rusefi/uaefi/boards/uaefi-a/board/-Produce_DanZhi.SMT_Snapshot.Bottom.2582135A_Y375.SMT02312031502790.png

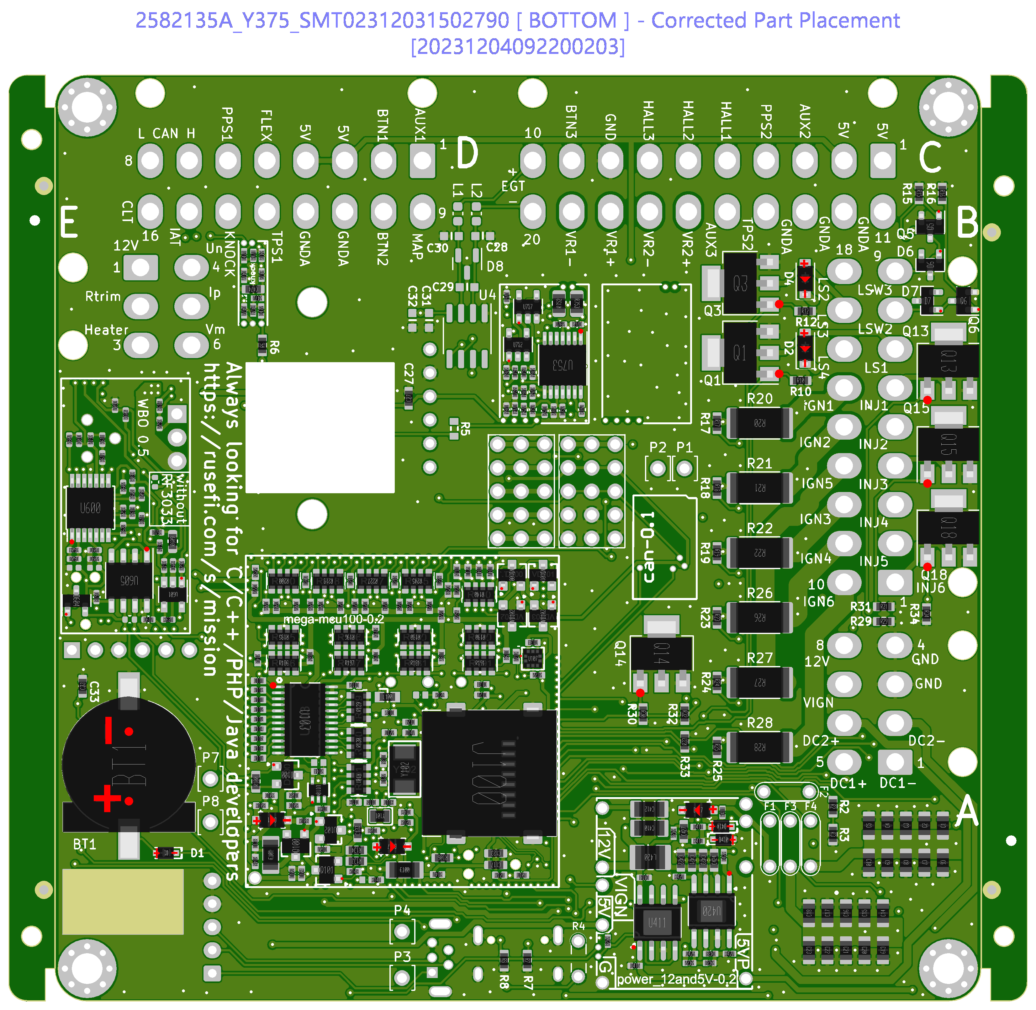
boards/uaefi-a/board/-Produce_DanZhi.SMT_Snapshot.Bottom.2582135A_Y375.SMT02312031502790.png
