rusefi/uaefi/boards/uaefi-a/board/misc/uaefi-a-bottom.png

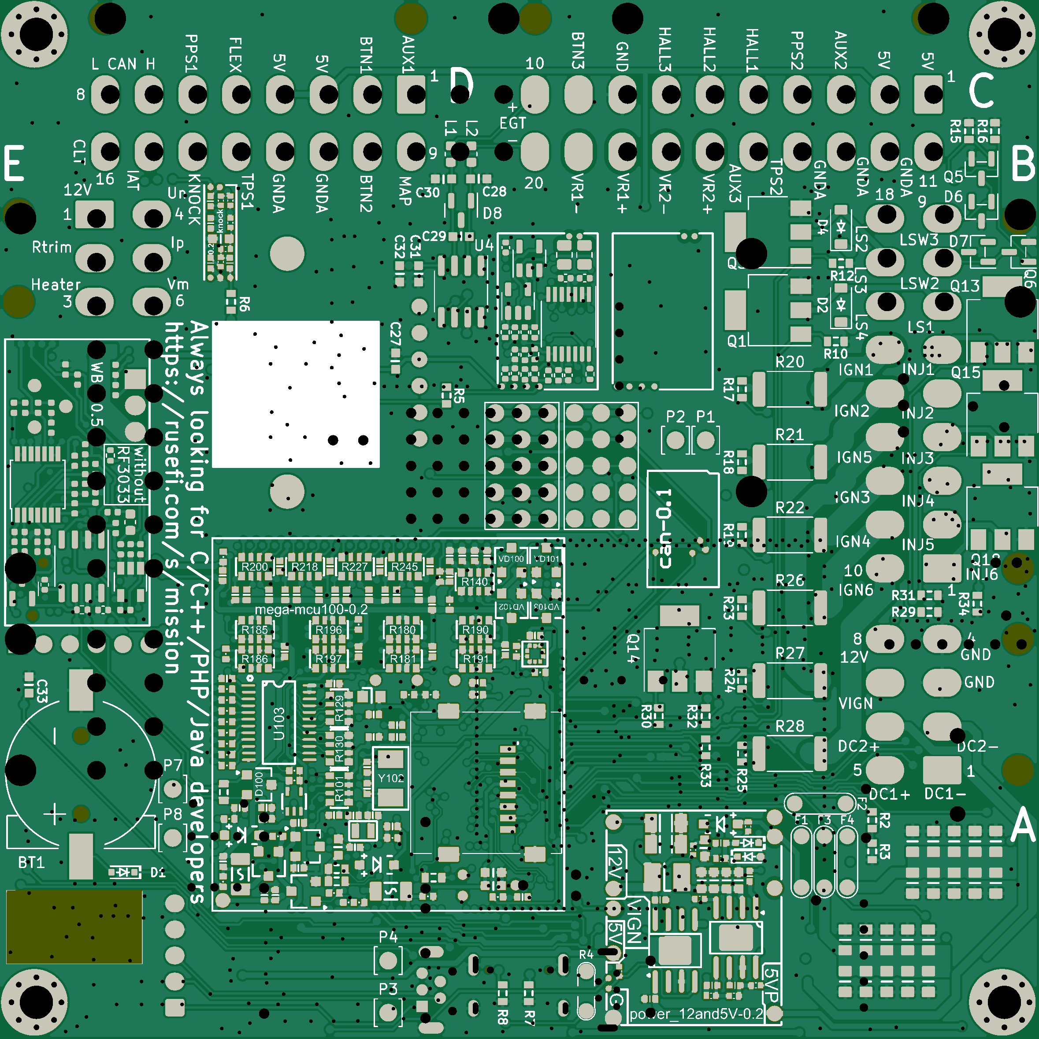
boards/uaefi-a/board/misc/uaefi-a-bottom.png
