rusefi/uaefi/boards/uaefi-a/board/misc/uaefi-a-top.png

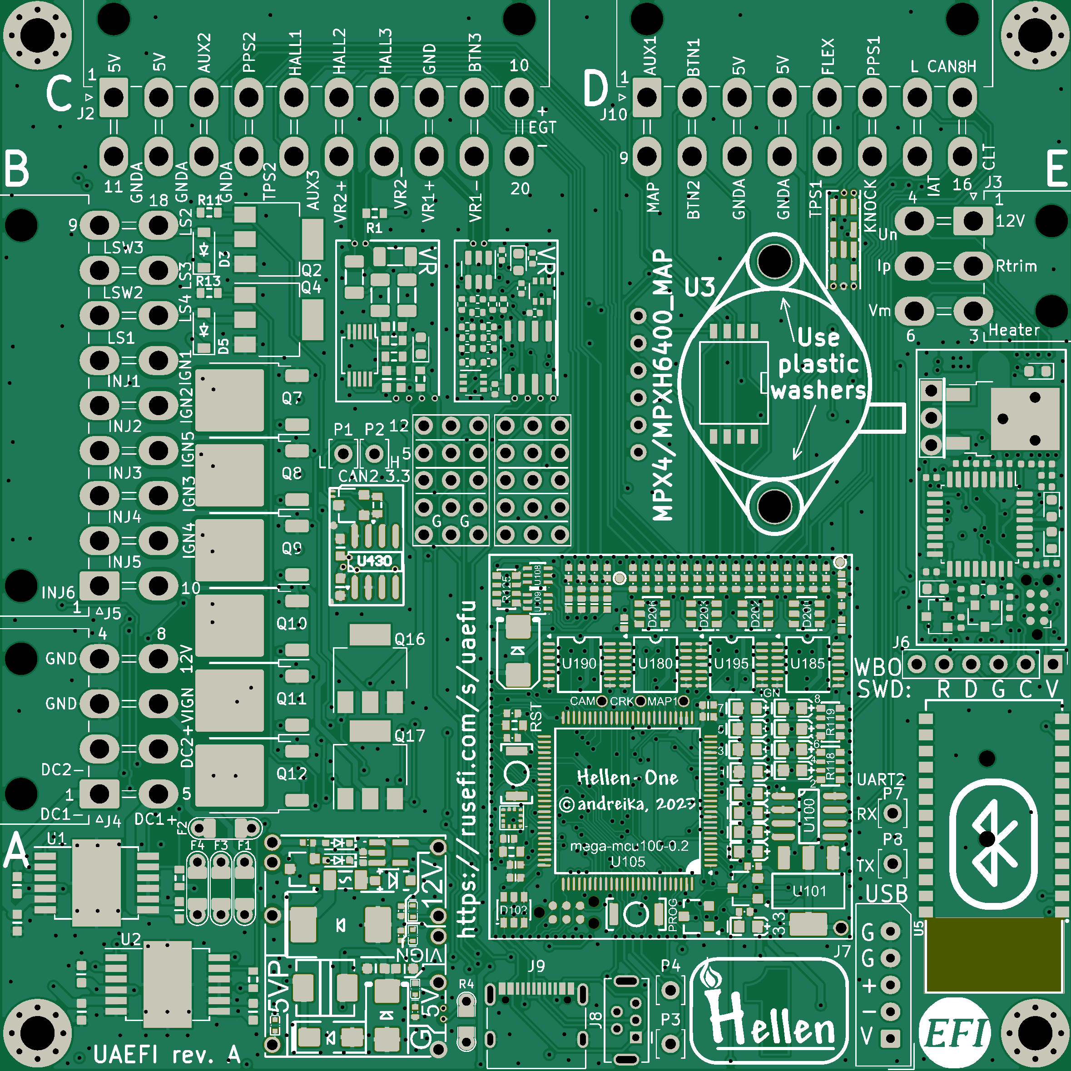
boards/uaefi-a/board/misc/uaefi-a-top.png
