rusefi/uaefi/boards/uaefi-a/board/uaefi-a.png

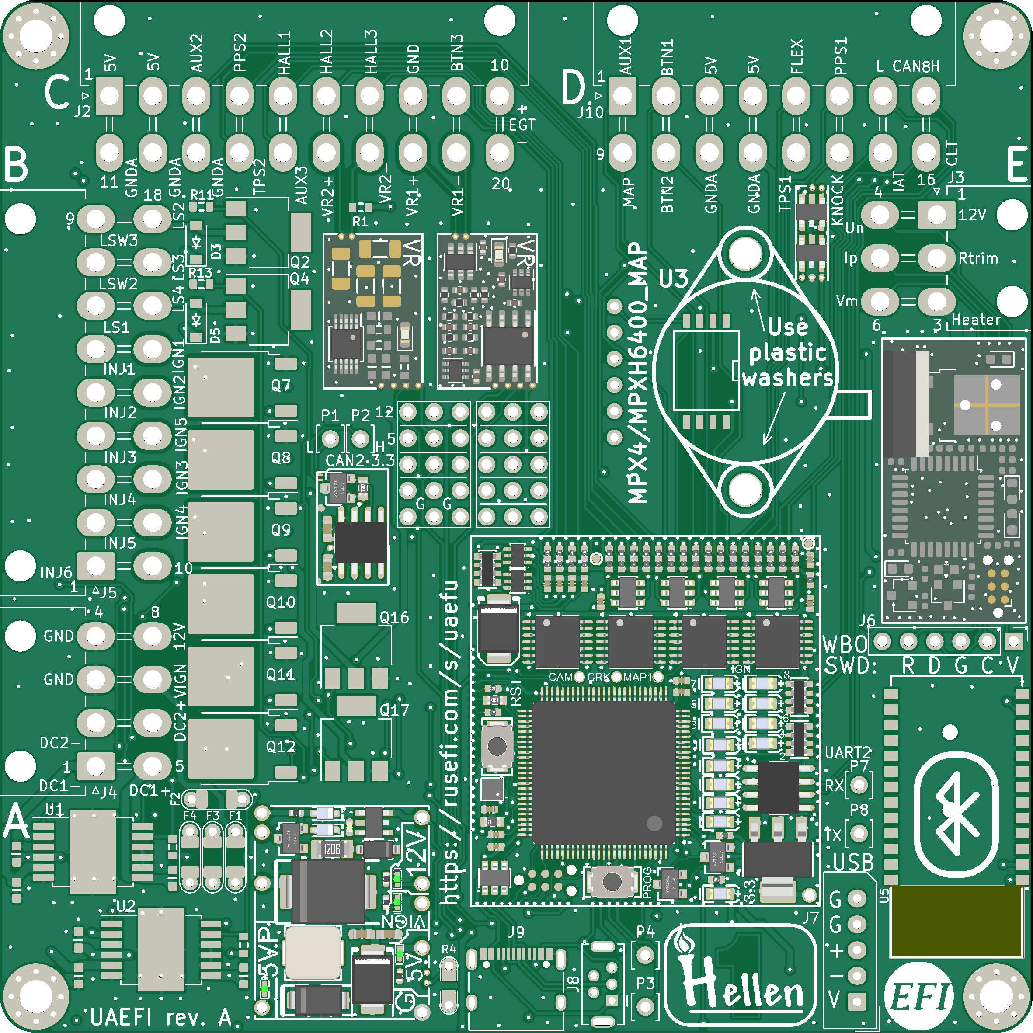
boards/uaefi-a/board/uaefi-a.png
