rusefi/uaefi/boards/uaefi-b/board/misc/uaefi-b-bottom.png

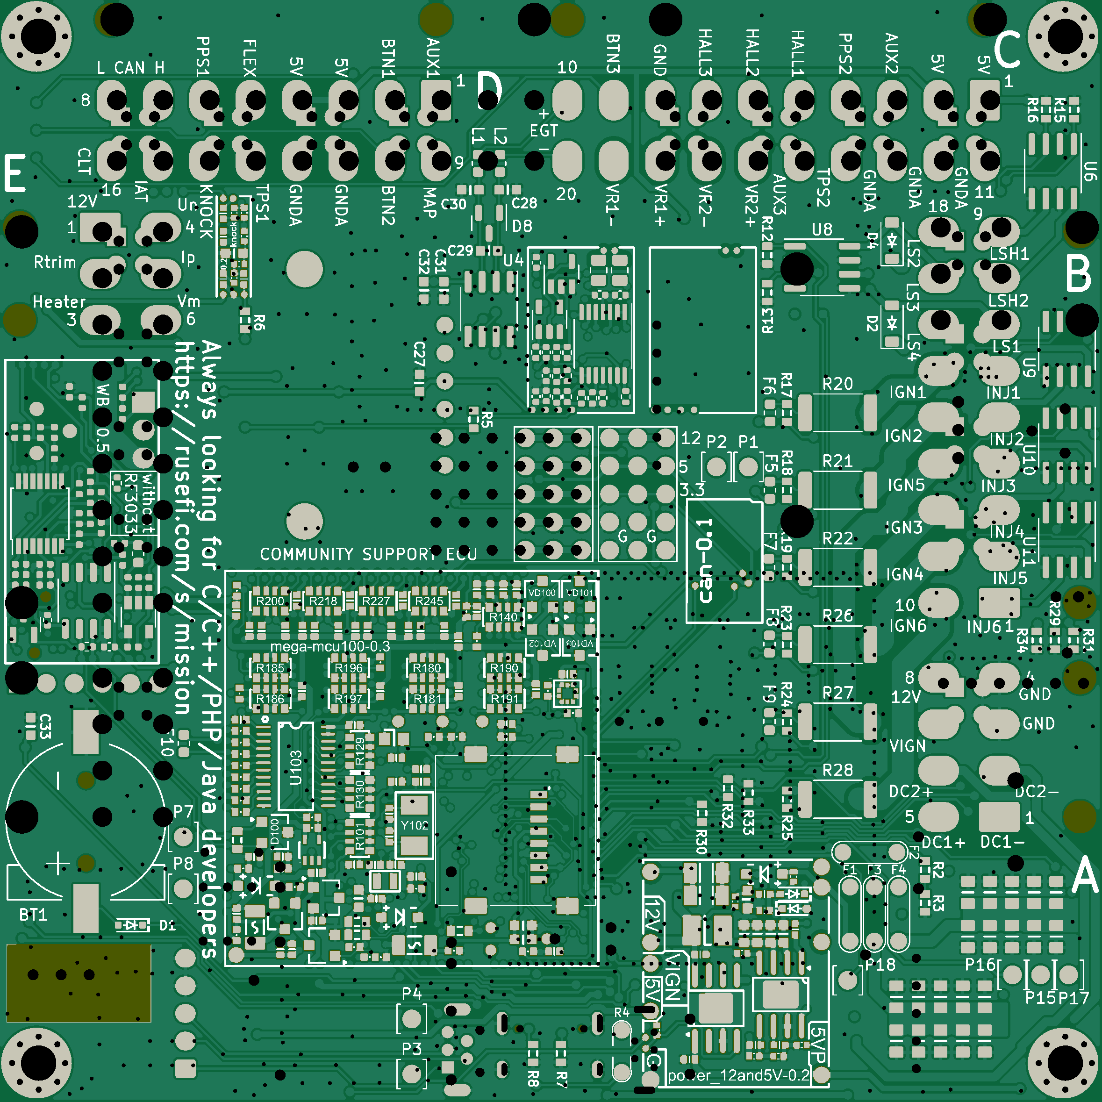
boards/uaefi-b/board/misc/uaefi-b-bottom.png
