rusefi/uaefi/boards/uaefi-b/board/misc/uaefi-b-outline.png

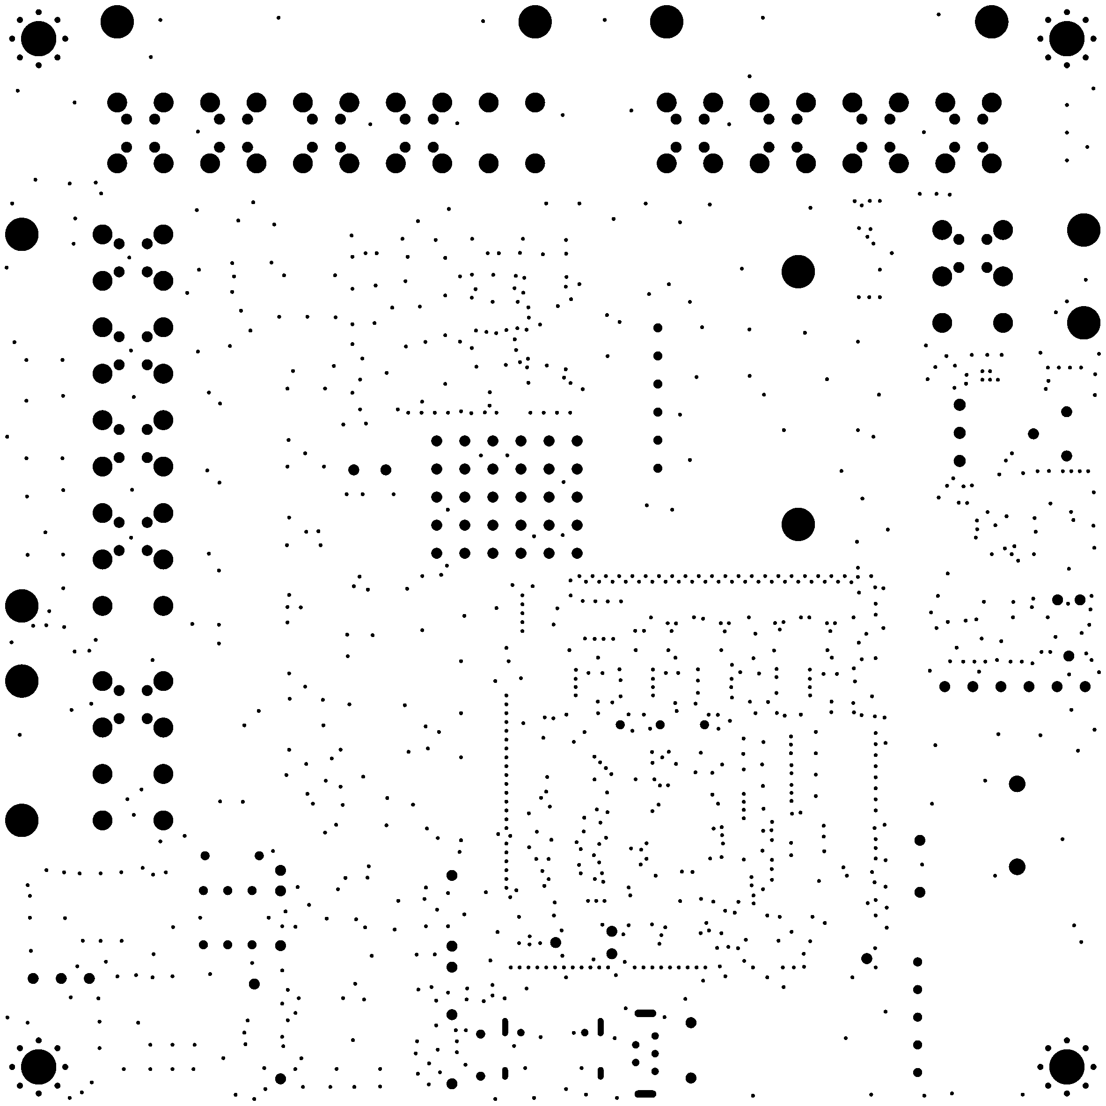
boards/uaefi-b/board/misc/uaefi-b-outline.png
