rusefi/uaefi/boards/uaefi-b/board/misc/uaefi-b-top.png

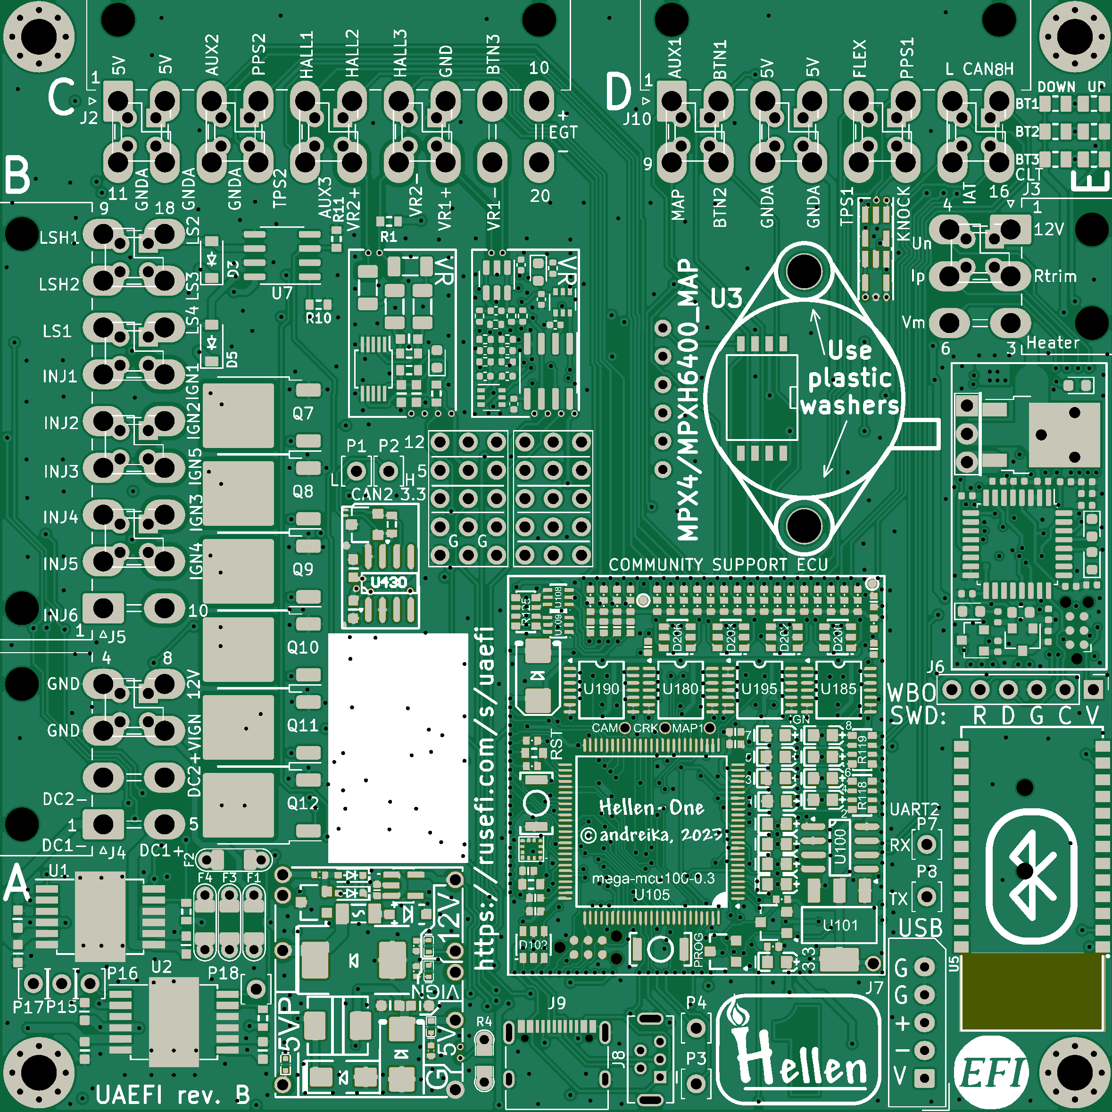
boards/uaefi-b/board/misc/uaefi-b-top.png
