rusefi/uaefi/boards/uaefi-b/board/Produce_DanZhi.SMT_Original_Snapshot.Top.2582135A_Y401.SMT02402061592675.png

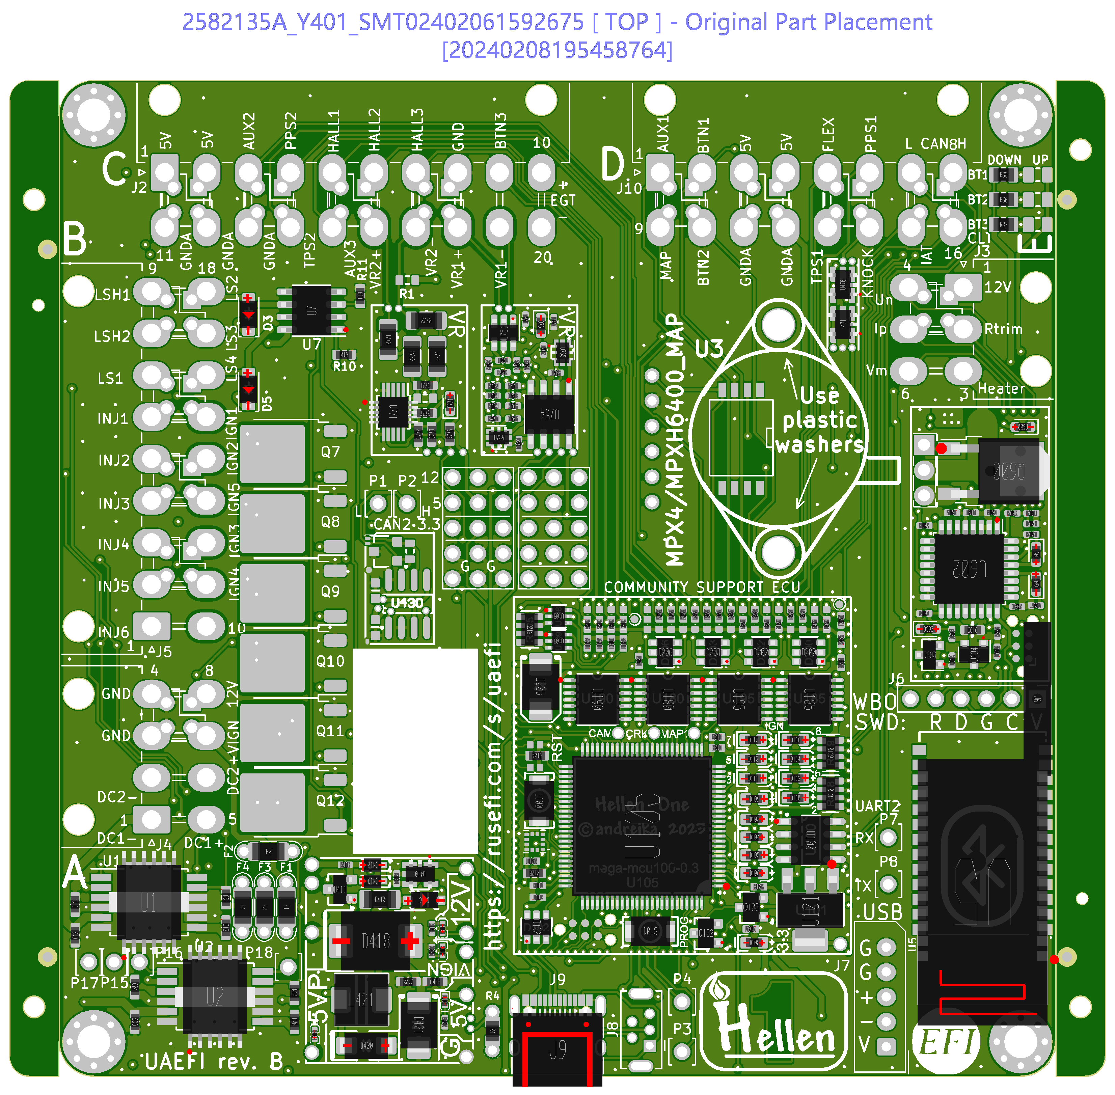
boards/uaefi-b/board/Produce_DanZhi.SMT_Original_Snapshot.Top.2582135A_Y401.SMT02402061592675.png
