rusefi/uaefi/boards/uaefi-b/board/uaefi-b.png

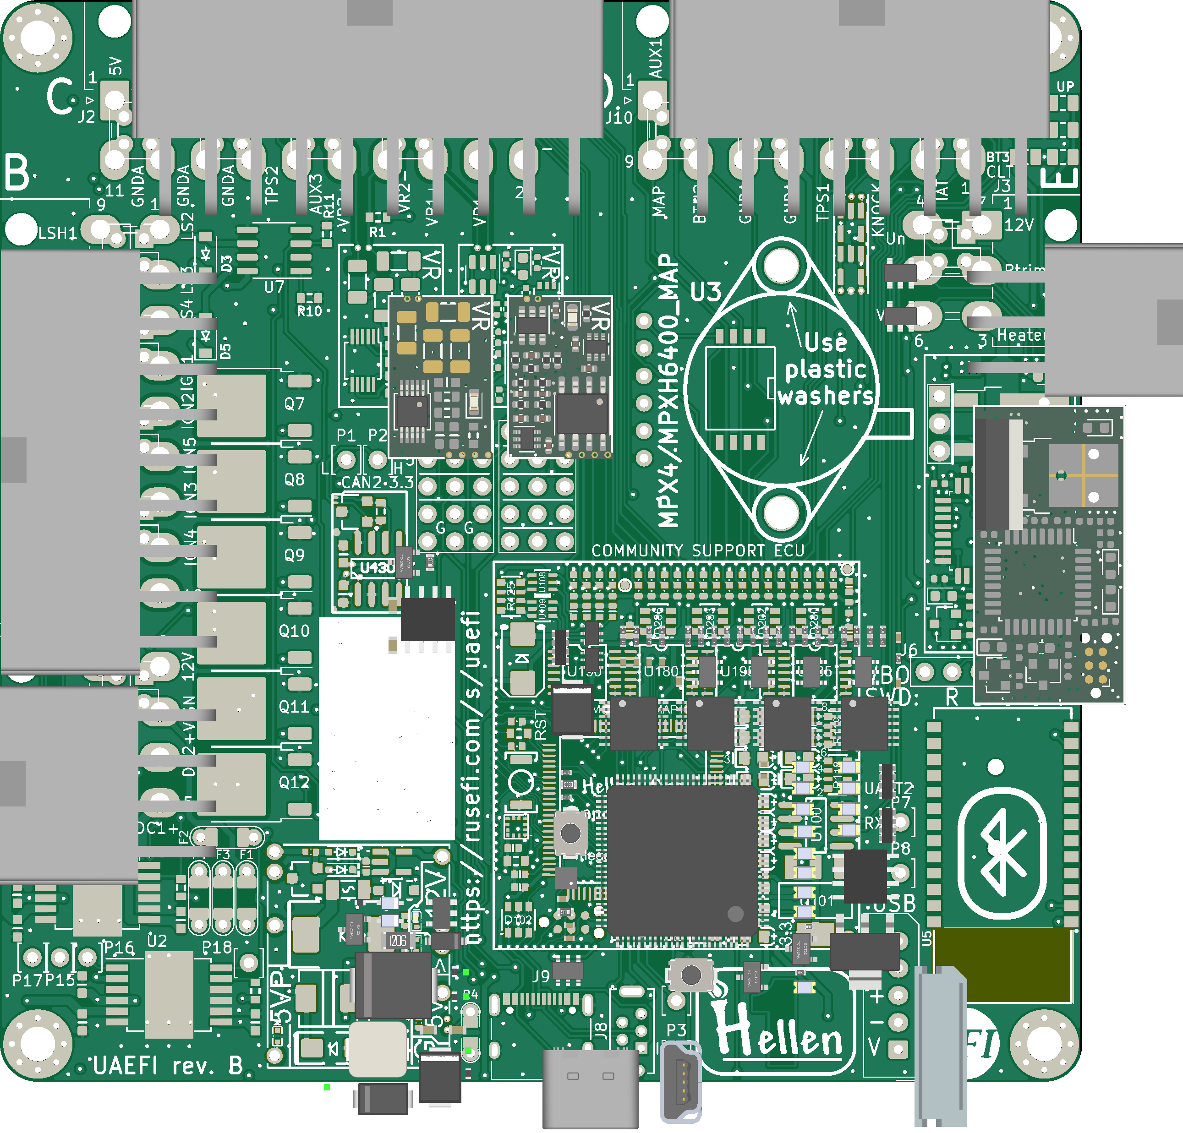
boards/uaefi-b/board/uaefi-b.png
