rusefi/uaefi/boards/uaefi-c/board/misc/uaefi-c-bottom.png

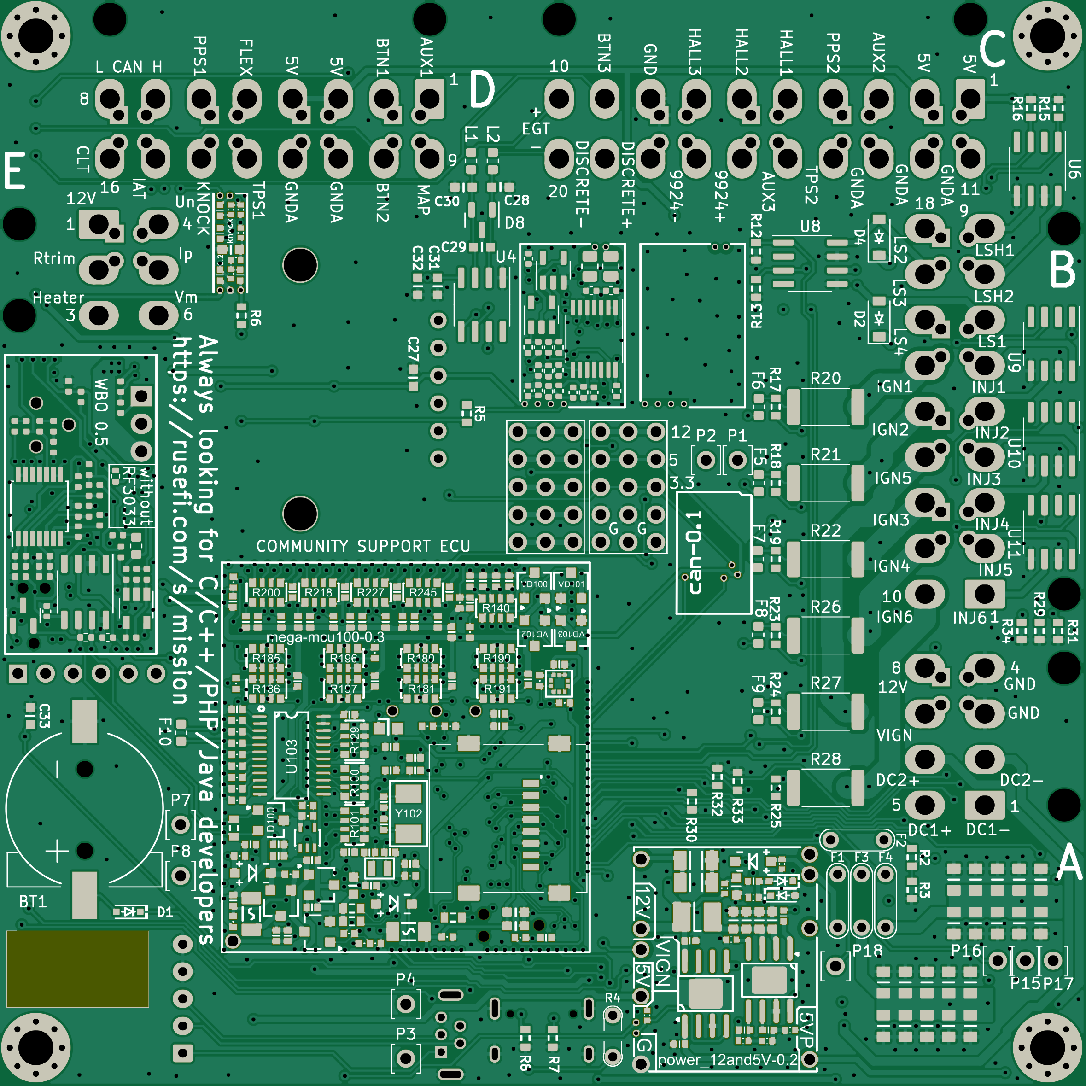
boards/uaefi-c/board/misc/uaefi-c-bottom.png
