rusefi/uaefi/boards/uaefi-c/board/misc/uaefi-c-top.png

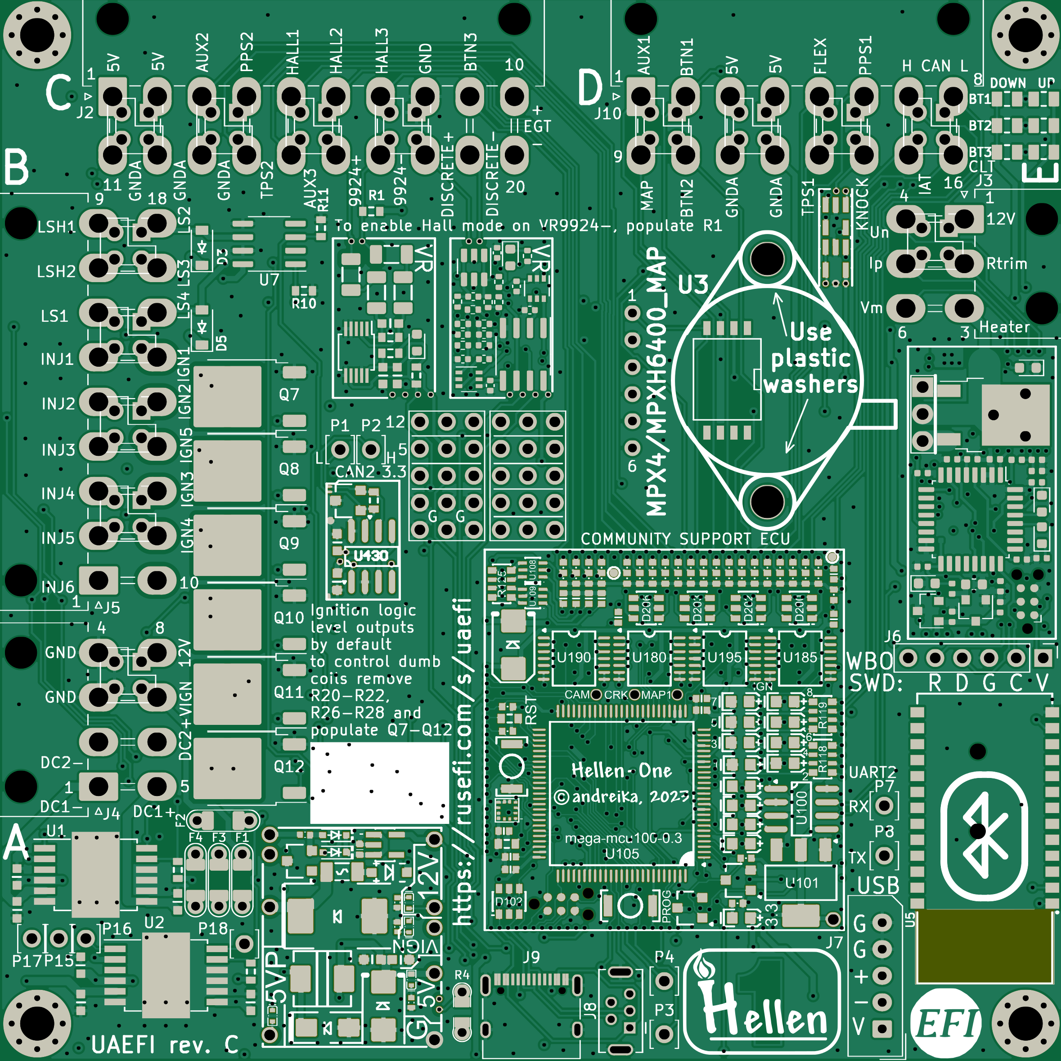
boards/uaefi-c/board/misc/uaefi-c-top.png
