rusefi/uaefi/boards/uaefi-c/board/Original_Snapshot.Top.2582135A_Y427.SMT02404051683002.png

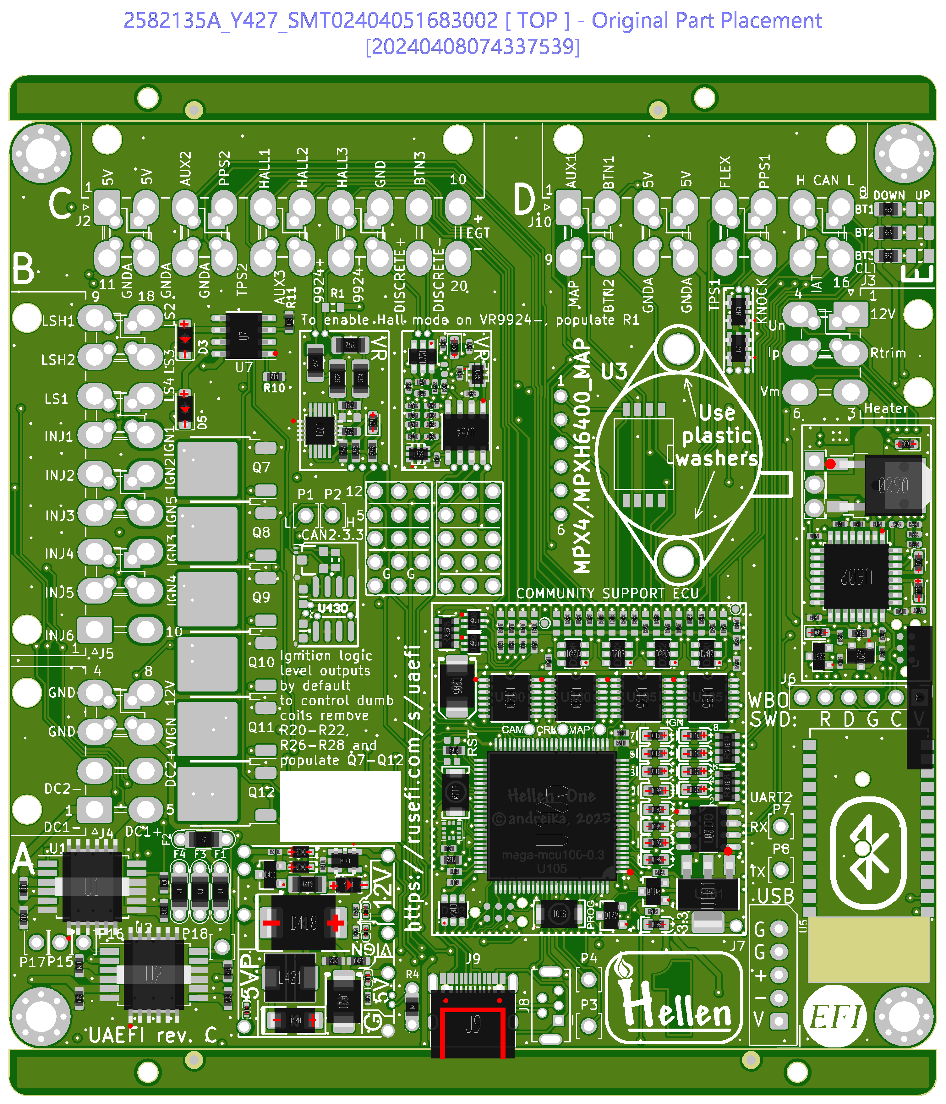
boards/uaefi-c/board/Original_Snapshot.Top.2582135A_Y427.SMT02404051683002.png
