rusefi/uaefi/boards/uaefi-c/board/Produce_DanZhi.SMT_Snapshot.Bottom.2582135A_Y427.SMT02404051683002.png

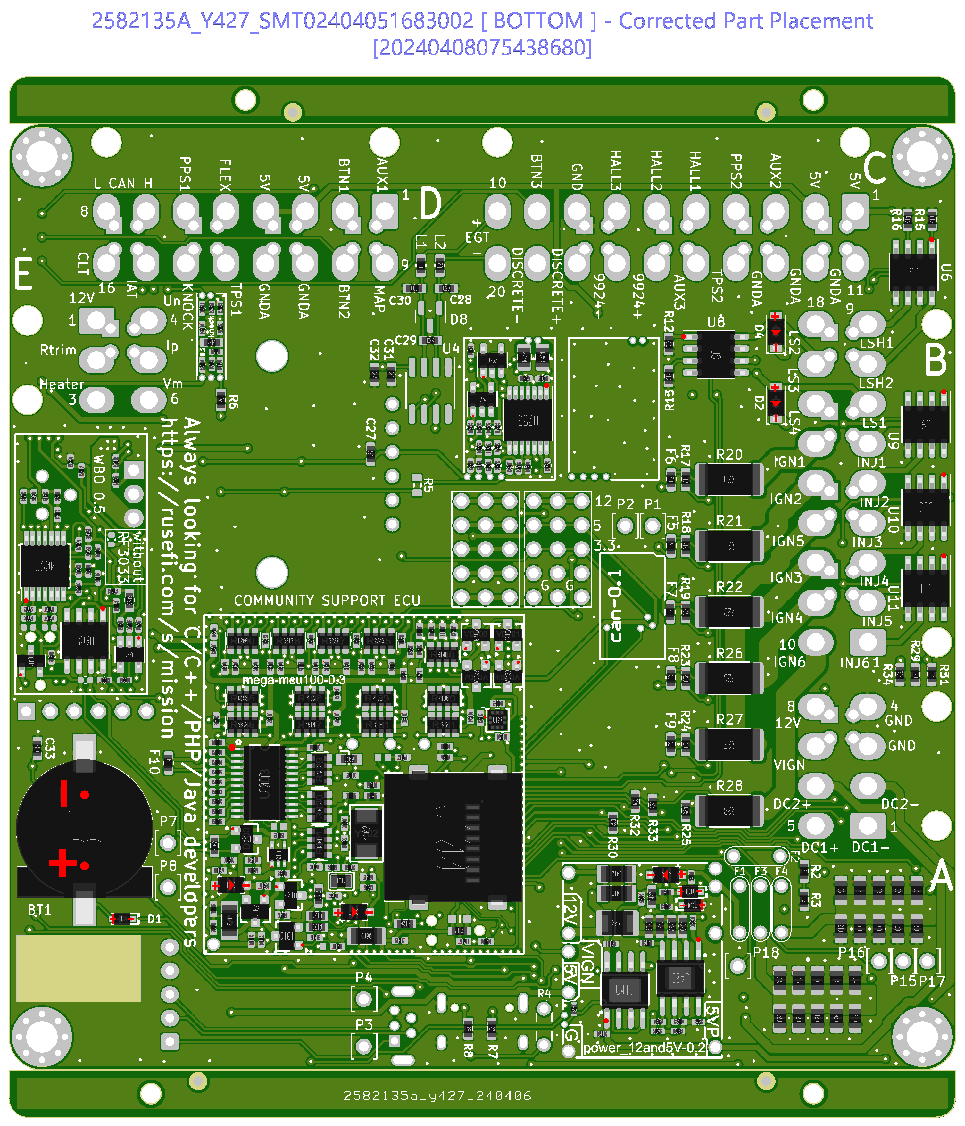
boards/uaefi-c/board/Produce_DanZhi.SMT_Snapshot.Bottom.2582135A_Y427.SMT02404051683002.png
