rusefi/uaefi/boards/uaefi-c/board/uaefi-c.png

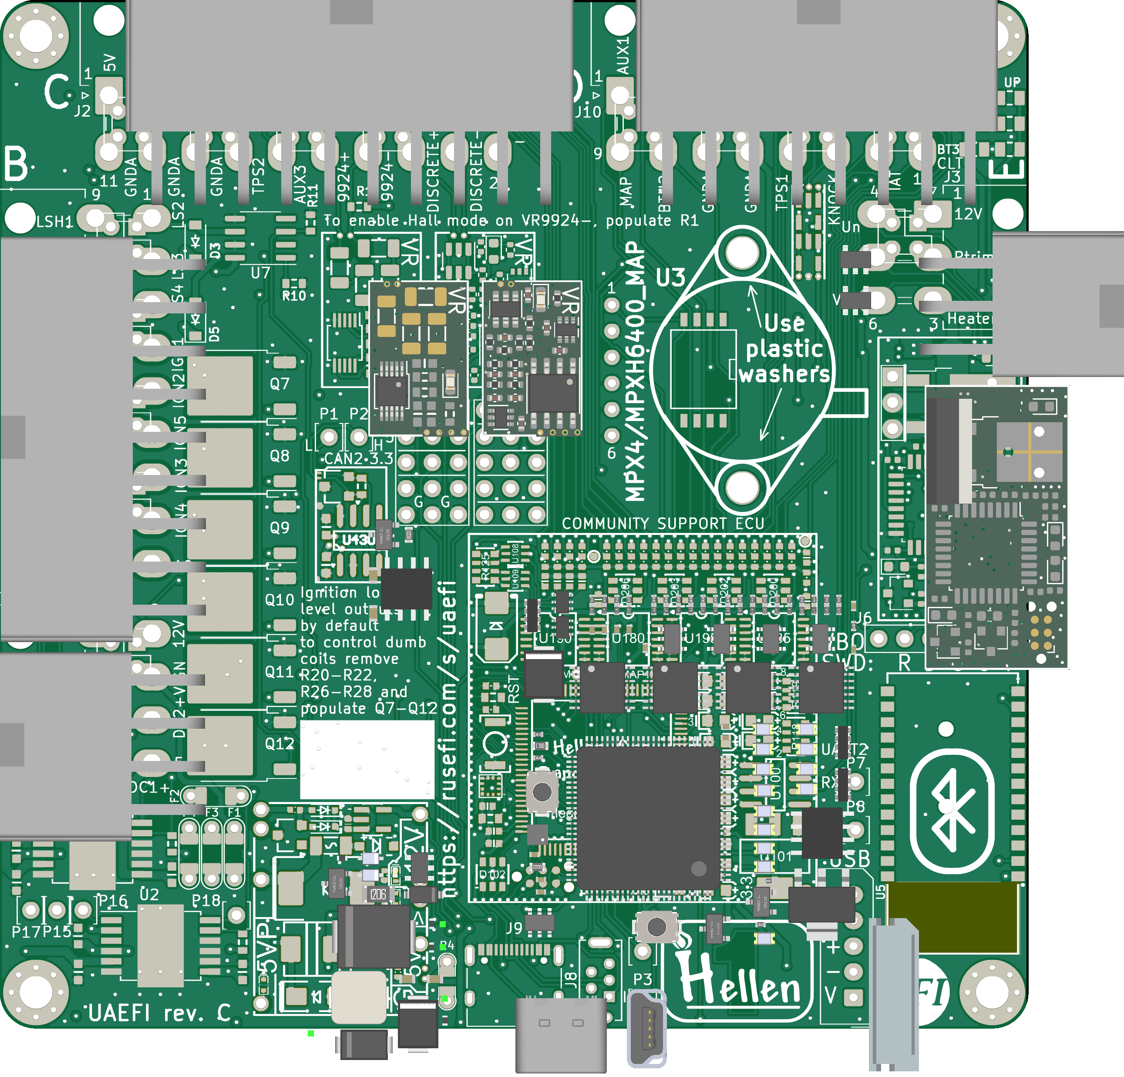
boards/uaefi-c/board/uaefi-c.png
