rusefi/uaefi/boards/uaefi-d/board/160-Produce_DanZhi.SMT_Original_Snapshot.Top.2582135A_Y468.SMT02408161894510.png

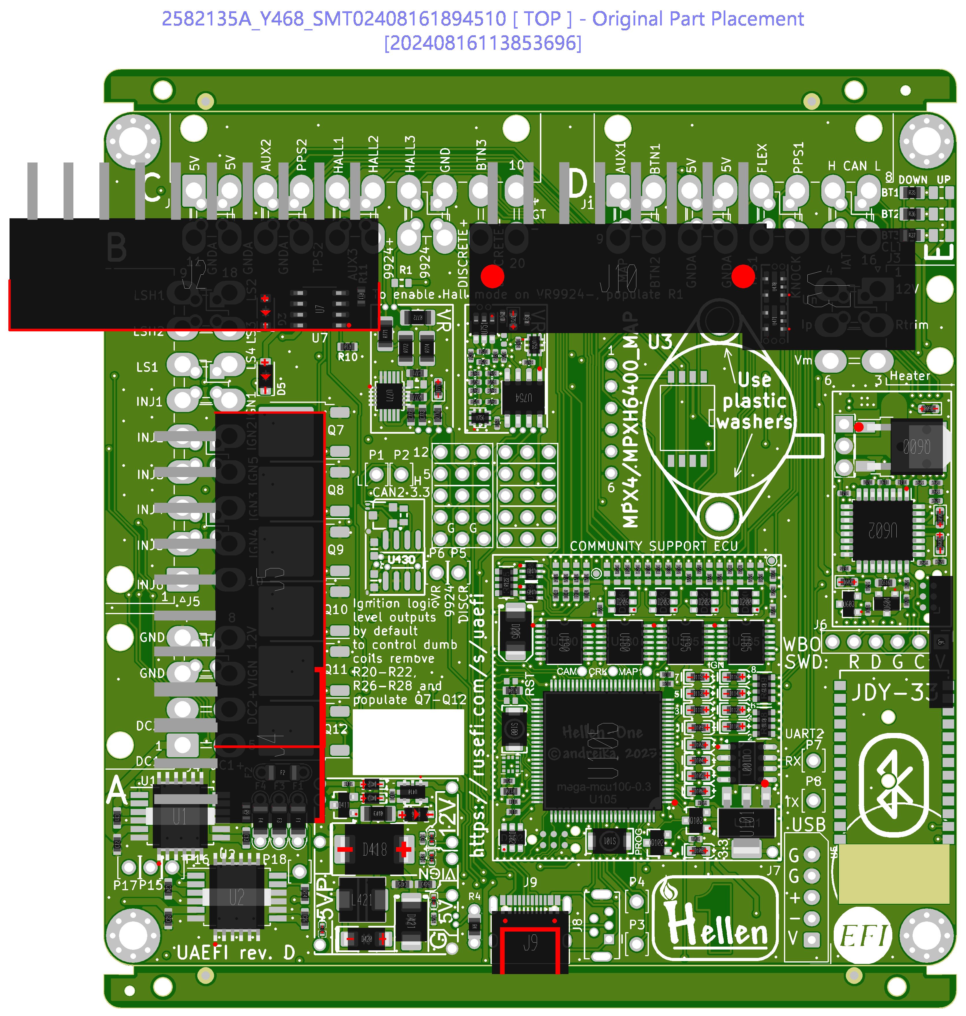
boards/uaefi-d/board/160-Produce_DanZhi.SMT_Original_Snapshot.Top.2582135A_Y468.SMT02408161894510.png
