rusefi/uaefi/boards/uaefi-d/board/119915741184-Produce_DanZhi.SMT_Snapshot.Top.2582135A_Y468.SMT02408161894510.png

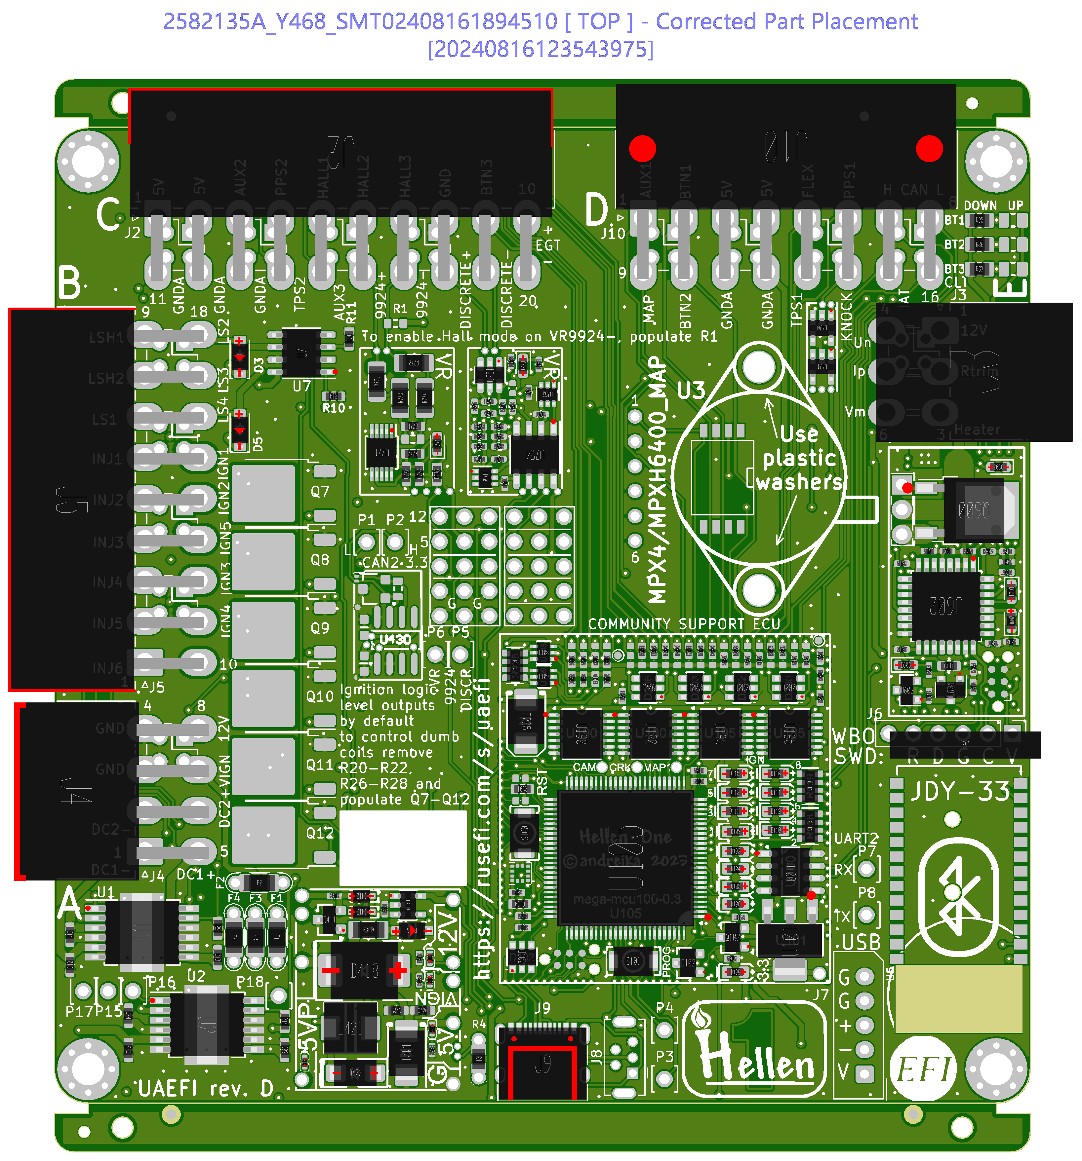
boards/uaefi-d/board/119915741184-Produce_DanZhi.SMT_Snapshot.Top.2582135A_Y468.SMT02408161894510.png
