rusefi/uaefi/boards/uaefi-d/board/-Produce_DanZhi.SMT_Original_Snapshot.Bottom.2582135A_Y468.SMT02408161894510.png

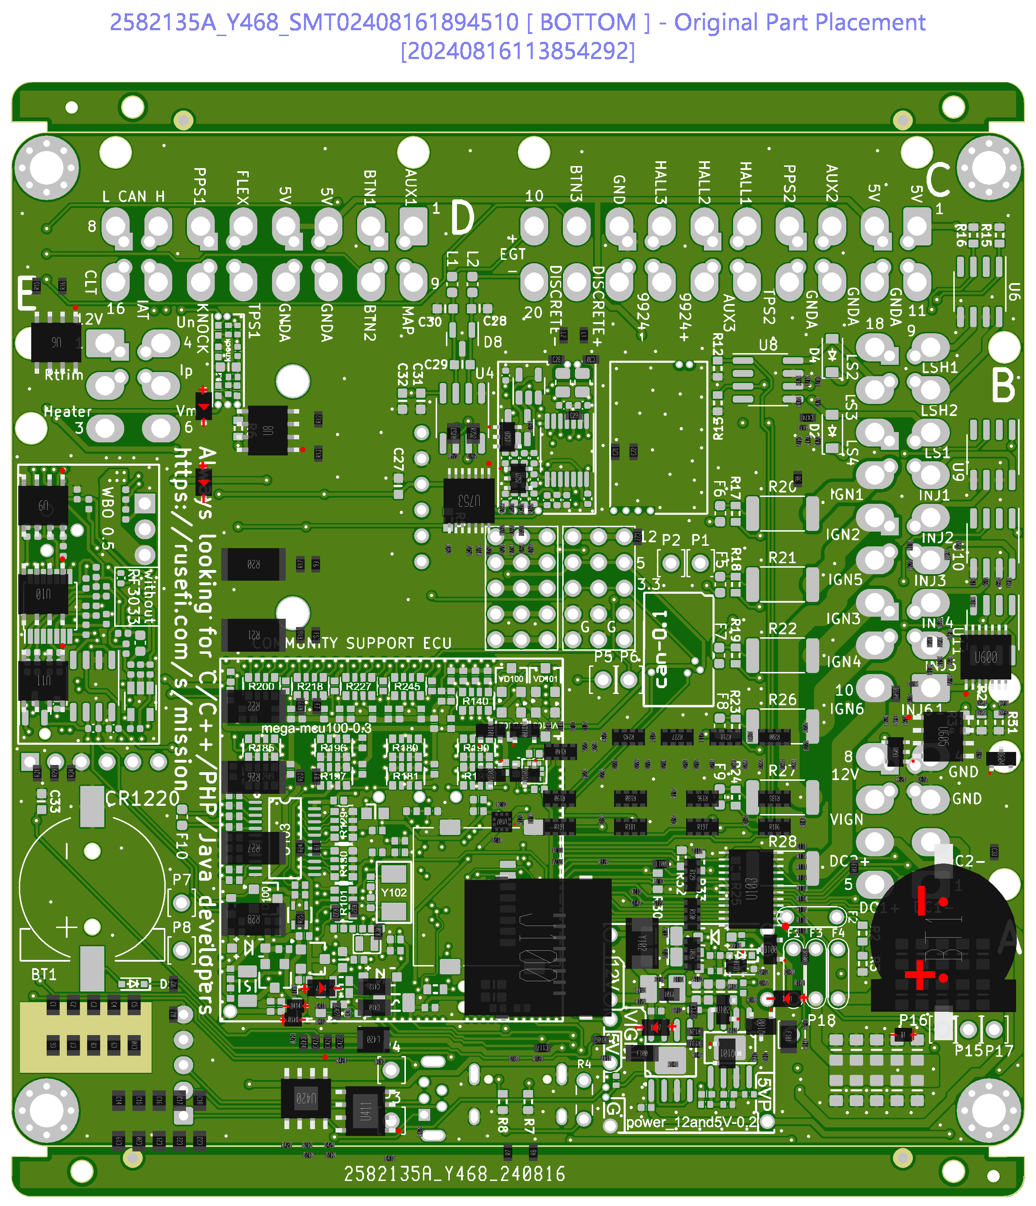
boards/uaefi-d/board/-Produce_DanZhi.SMT_Original_Snapshot.Bottom.2582135A_Y468.SMT02408161894510.png
