rusefi/uaefi/boards/uaefi-d/board/uaefi-d.png

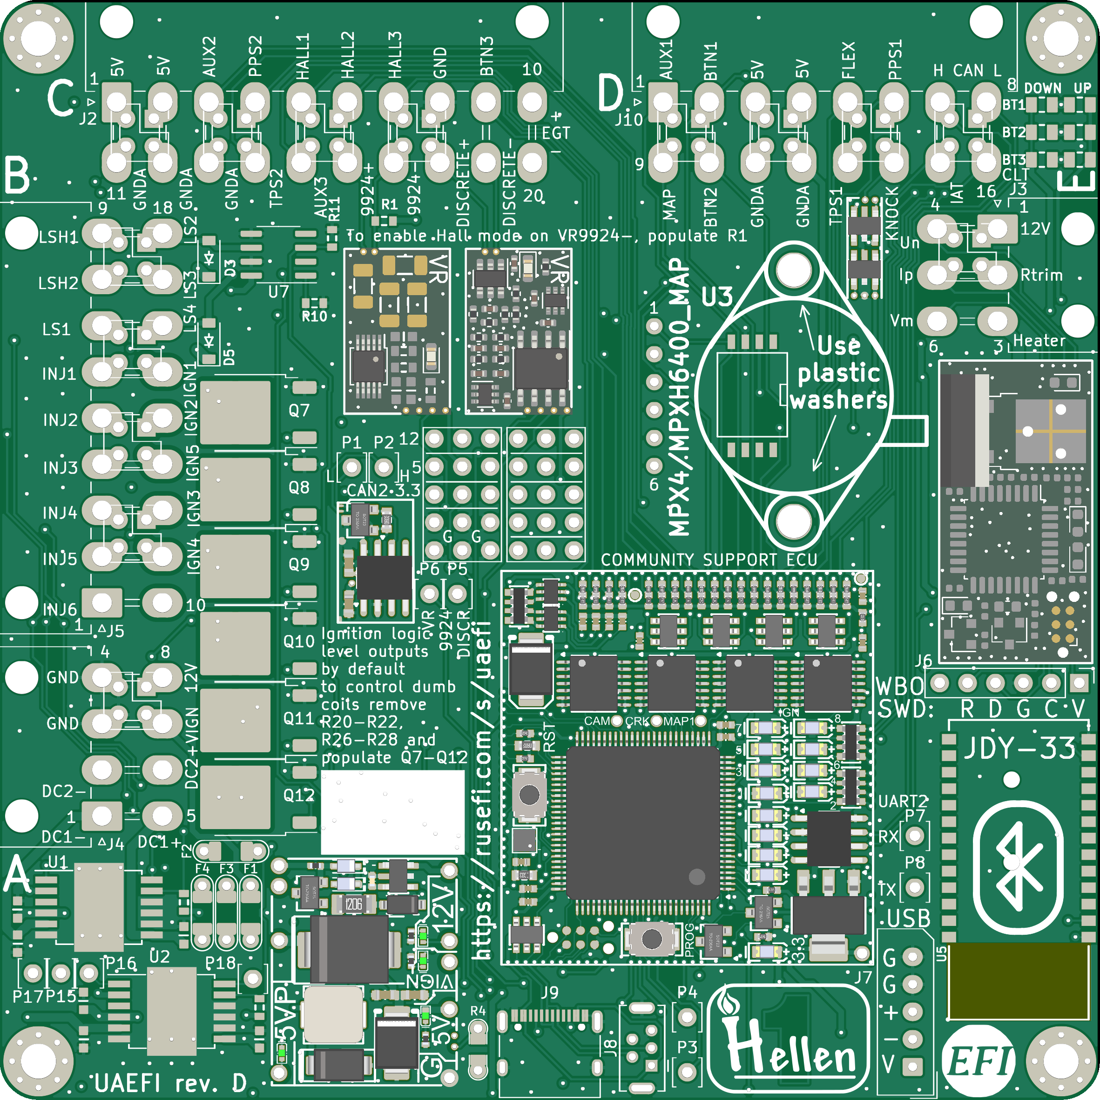
boards/uaefi-d/board/uaefi-d.png
