rusefi/uaefi/boards/uaefi-e2/board/misc/uaefi-e2-outline.png

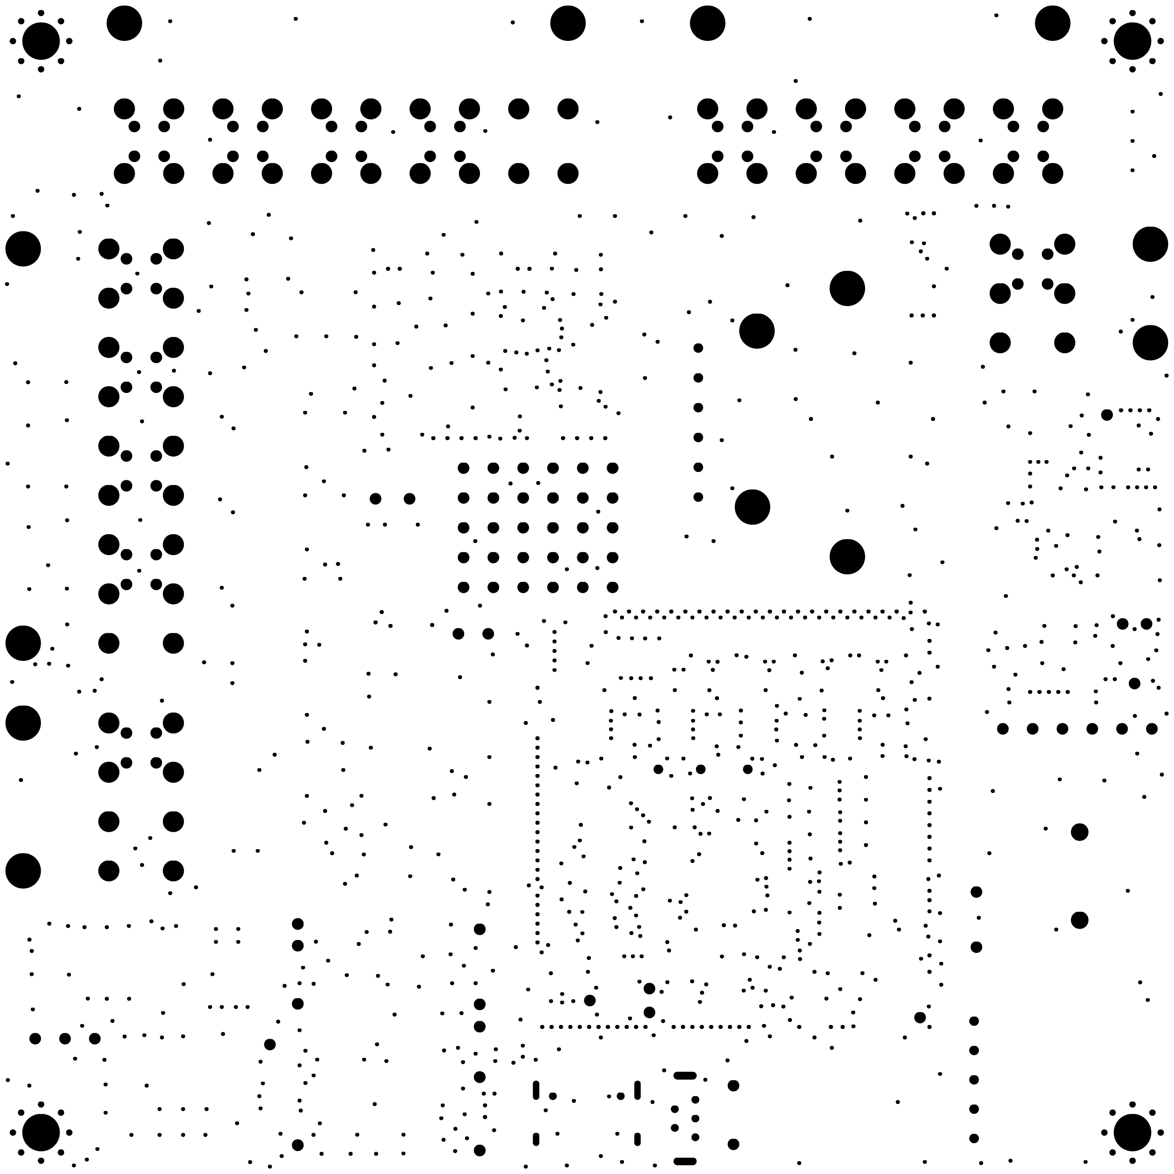
boards/uaefi-e2/board/misc/uaefi-e2-outline.png
