rusefi/uaefi/boards/uaefi-f2/board/misc/uaefi-f2-bottom.png

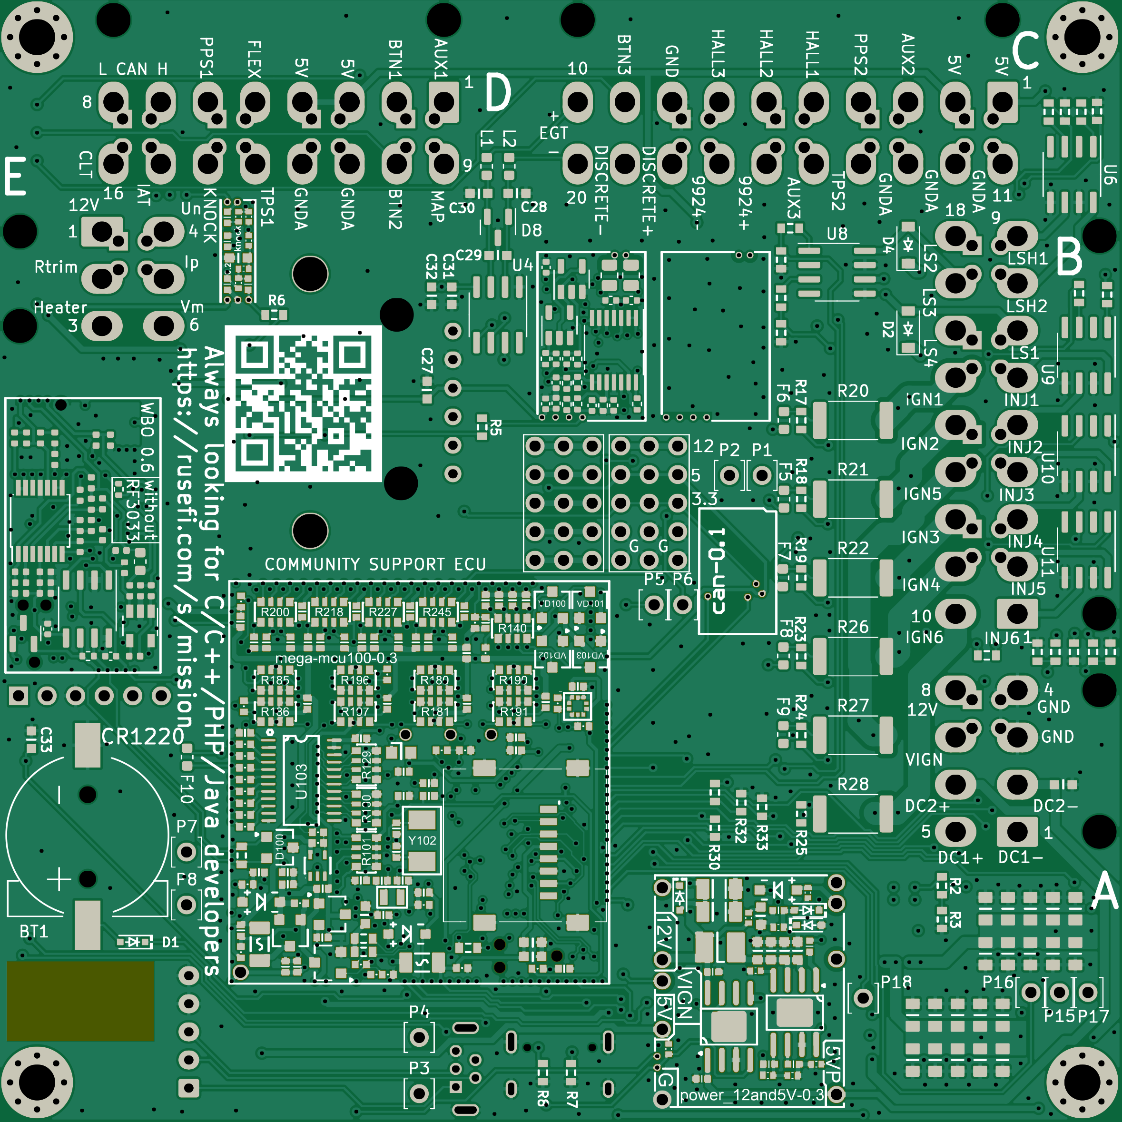
boards/uaefi-f2/board/misc/uaefi-f2-bottom.png
