rusefi/uaefi/boards/uaefi-f2/board/misc/uaefi-f2-top.png

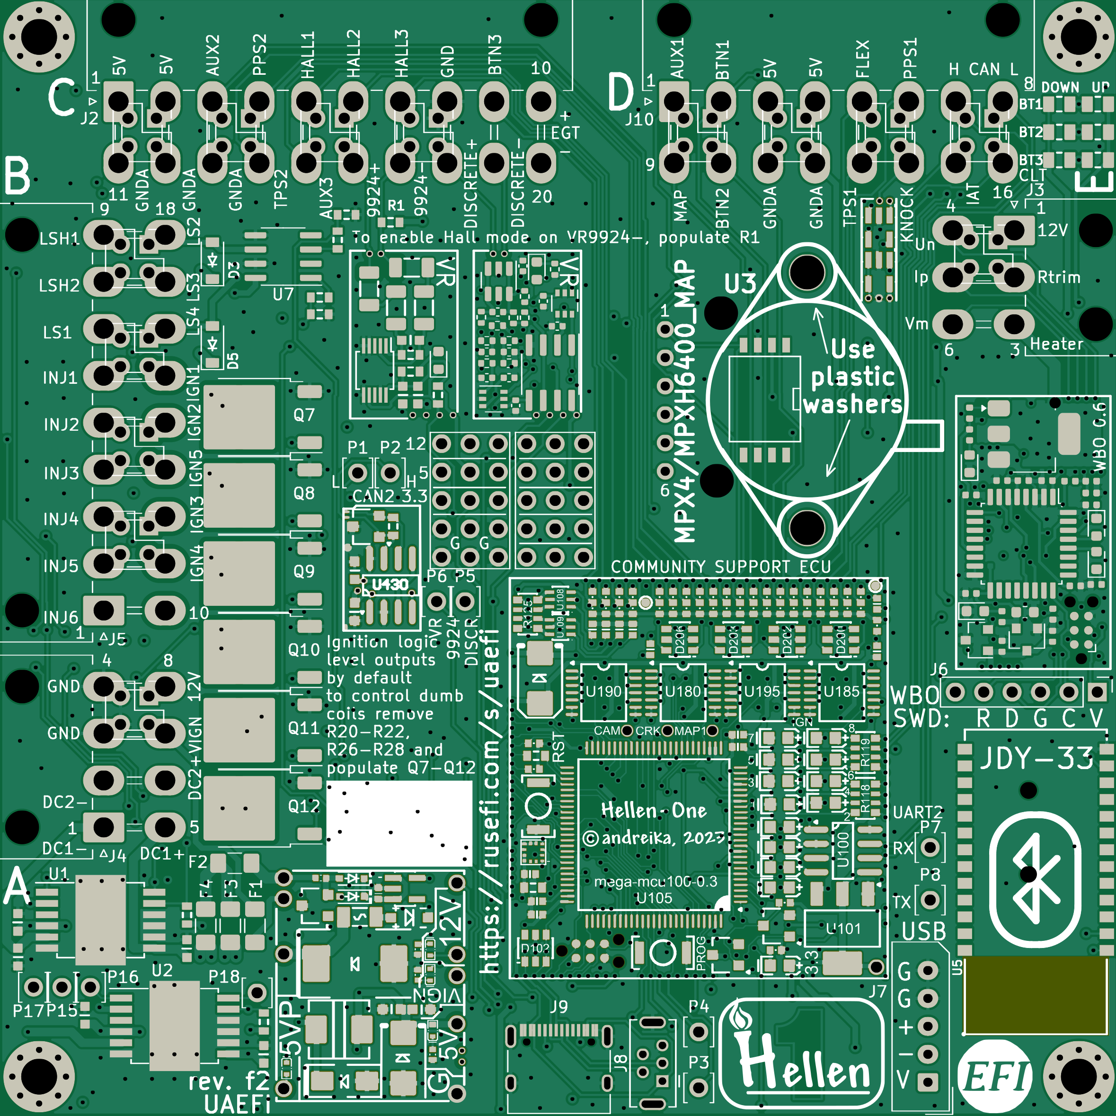
boards/uaefi-f2/board/misc/uaefi-f2-top.png
