rusefi/uaefi/boards/uaefi-f3/board/uaefi-f3.png

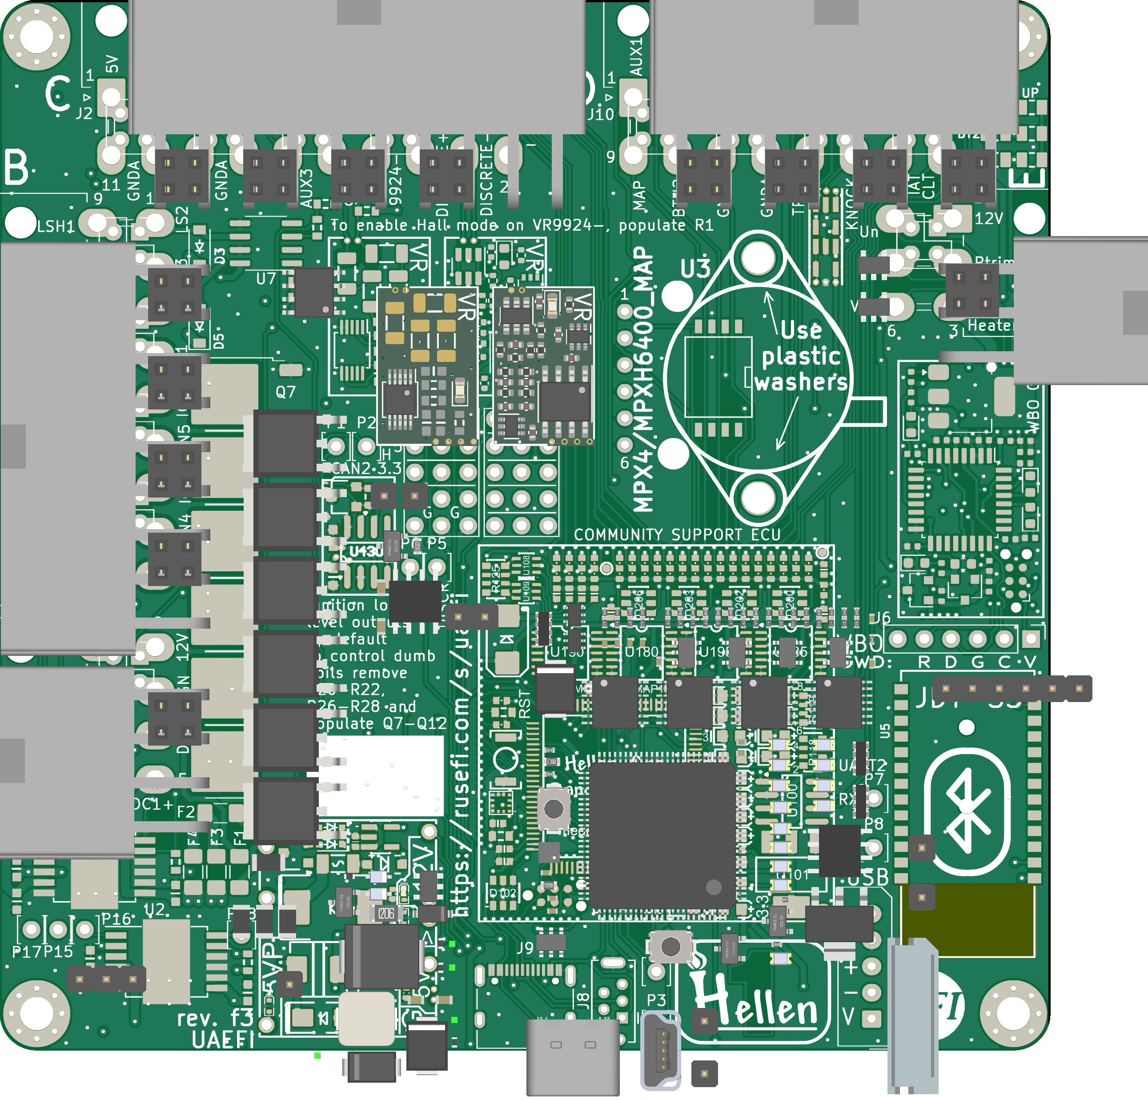
boards/uaefi-f3/board/uaefi-f3.png
