rusefi/uaefi/docs/base-top.jpg

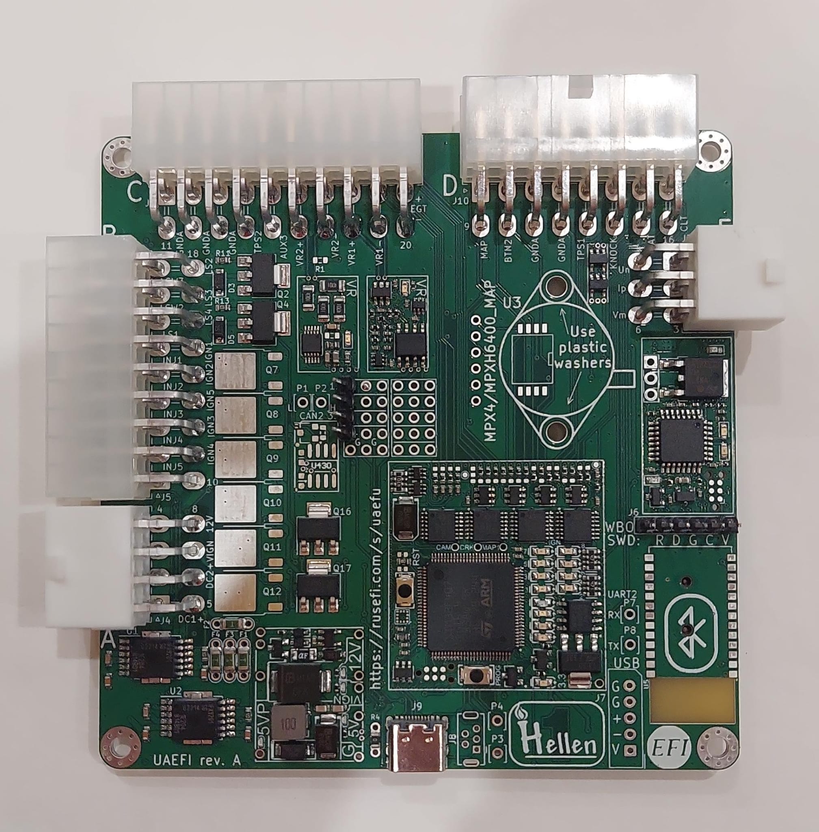
docs/base-top.jpg
