rusefi/uaefi/docs/orange.jpg

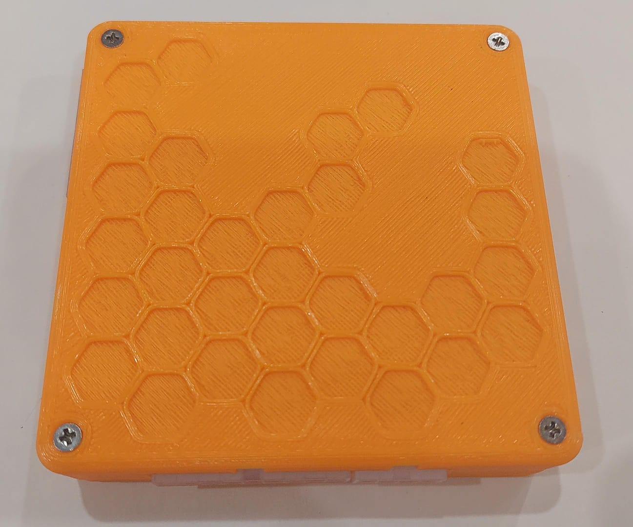
docs/orange.jpg
