rusefi/uaefi/docs/premium-bottom.jpg

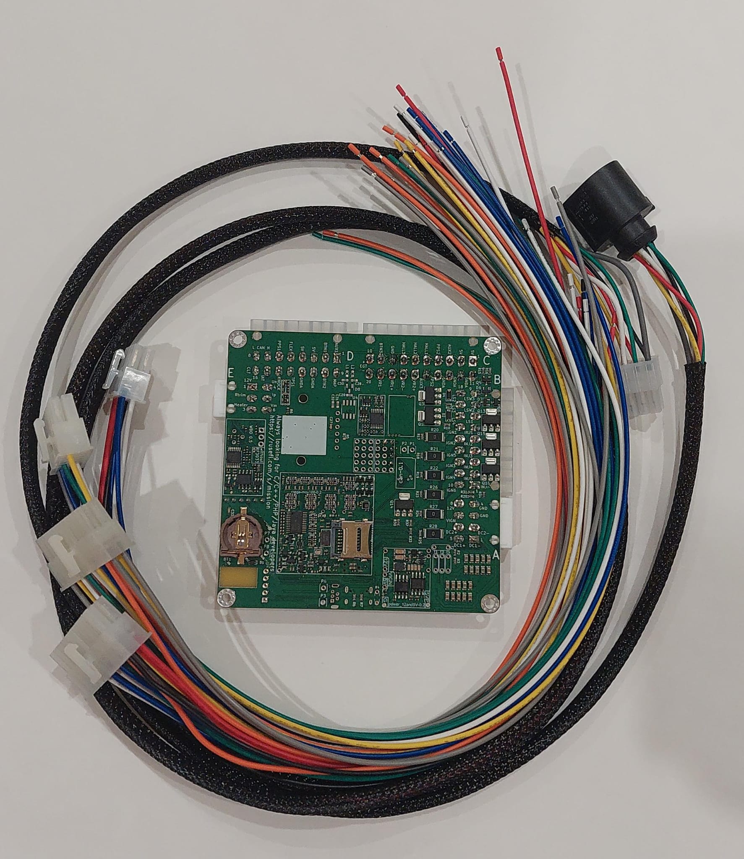
docs/premium-bottom.jpg
