rusefi/uaefi/docs/premium-top.jpg

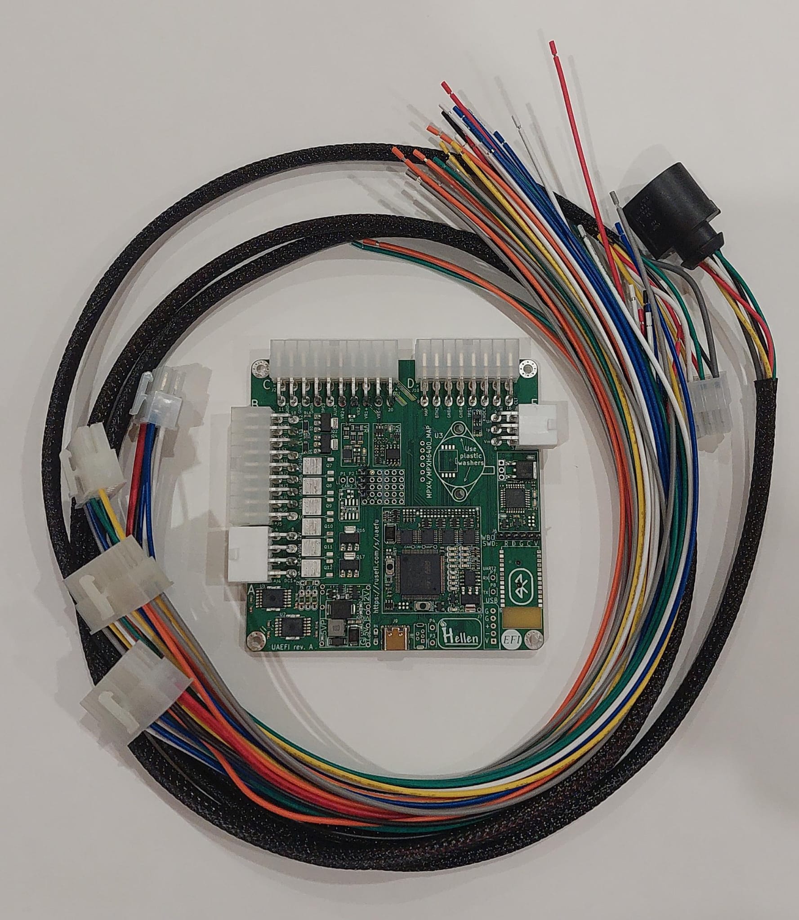
docs/premium-top.jpg
