rusefi/uaefi/boards/uaefi-f3/frame/efi-BOM.csv

Comment | Designator | Footprint | LCSC Part #
CR1220 | BT1 | CR1220-2 | C70381
10u | C1 | C0805 | C15850
10u | C2 | C0805 | C15850
10u | C3 | C0805 | C15850
10u | C4 | C0805 | C15850
10u | C5 | C0805 | C15850
10u | C6 | C0805 | C15850
10u | C7 | C0805 | C15850
10u | C8 | C0805 | C15850
10u | C9 | C0805 | C15850
10u | C10 | C0805 | C15850
100n | C11 | C0603 | C14663
10n | C12 | C0603 | C57112
10n | C13 | C0603 | C57112
10u | C14 | C0805 | C15850
10u | C15 | C0805 | C15850
10u | C16 | C0805 | C15850
10u | C17 | C0805 | C15850
10u | C18 | C0805 | C15850
10u | C19 | C0805 | C15850
10u | C20 | C0805 | C15850
10u | C21 | C0805 | C15850
10u | C22 | C0805 | C15850
10u | C23 | C0805 | C15850
100n | C24 | C0603 | C14663
10n | C25 | C0603 | C57112
10n | C26 | C0603 | C57112
100n | C27 | C0603 | C14663
10n | C28 | C0603 | C57112
100n | C29 | C0603 | C14663
10n | C30 | C0603 | C57112
100n | C31 | C0603 | C14663
1u | C32 | C0603 | C15849
100n | C33 | C0603 | C14663
1N4148WS | D1 | SOD-323 | C2128
B5819W | D2 | SOD-123 | C8598
B5819W | D3 | SOD-123 | C8598
B5819W | D4 | SOD-123 | C8598
B5819W | D5 | SOD-123 | C8598
NUP2105L | D8 | SOT-23 | C284104
Fuse | F1 | Fuse_1206_3216Metric_Pad1.42x1.75mm_HandSolder | C182446
Fuse | F2 | Fuse_1206_3216Metric_Pad1.42x1.75mm_HandSolder | C182446
Fuse | F3 | Fuse_1206_3216Metric_Pad1.42x1.75mm_HandSolder | C182446
Fuse | F4 | Fuse_1206_3216Metric_Pad1.42x1.75mm_HandSolder | C182446
50mA | F5 | Fuse_0603_1608Metric | C369141
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
MAX31855KASA | U4 | SO8 | C52028
JDY-33 | U5 | JDY-33 | C9900001612
VNLD5160TR-E | U6 | SO8 | C377942
VNLD5160TR-E | U7 | SO8 | C377942
VNLD5160TR-E | U8 | SO8 | C377942
VNLD5160TR-E | U9 | SO8 | C377942
VNLD5160TR-E | U10 | SO8 | C377942
VNLD5160TR-E | U11 | SO8 | C377942
