rusefi/uaefi/boards/uaefi-b/board/misc/uaefi-b-components.png

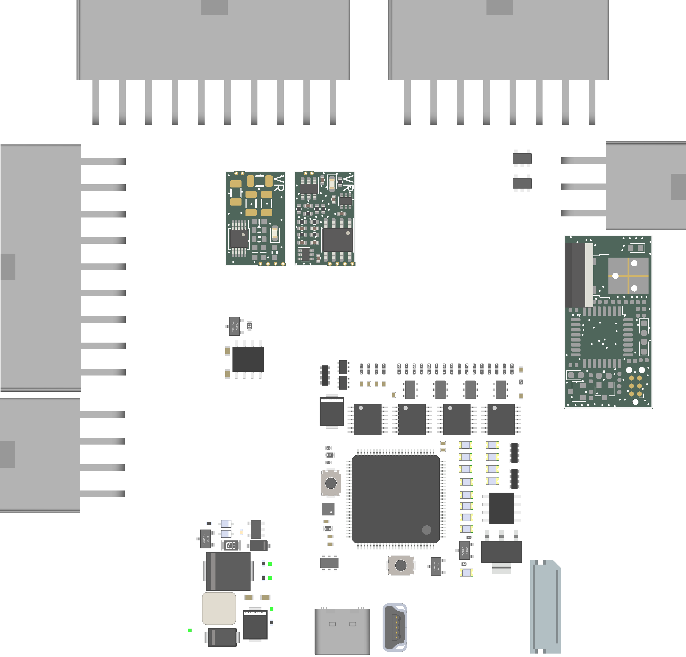
boards/uaefi-b/board/misc/uaefi-b-components.png
