rusefi/uaefi/boards/uaefi-c/board/misc/uaefi-c-components.png

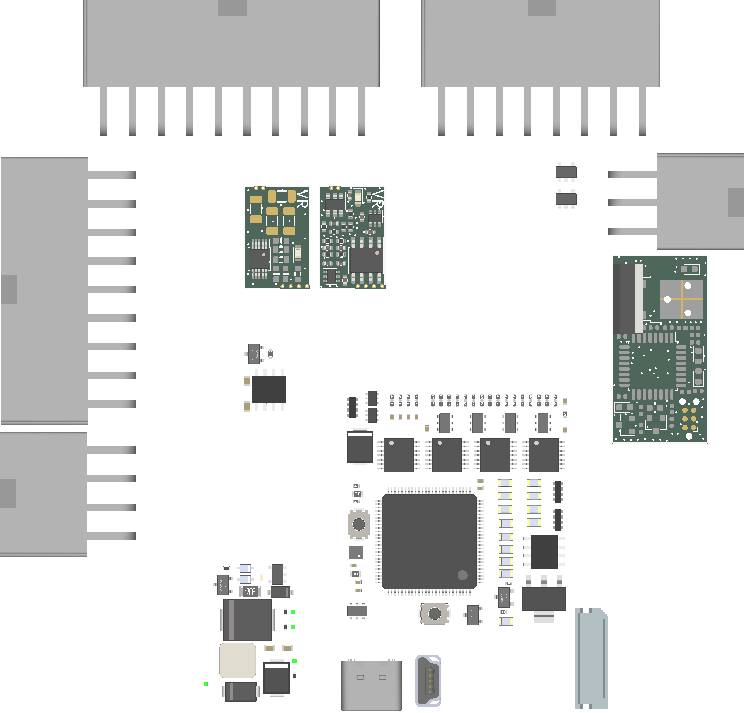
boards/uaefi-c/board/misc/uaefi-c-components.png
