rusefi/uaefi/boards/uaefi-e/board/misc/uaefi-e-components.png

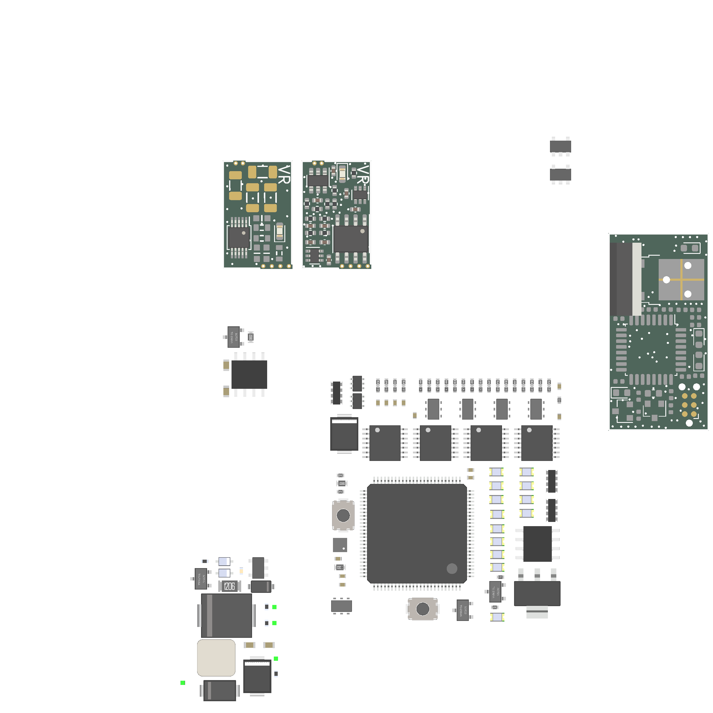
boards/uaefi-e/board/misc/uaefi-e-components.png
