rusefi/uaefi/boards/uaefi-f3/board/misc/uaefi-f3-components.png

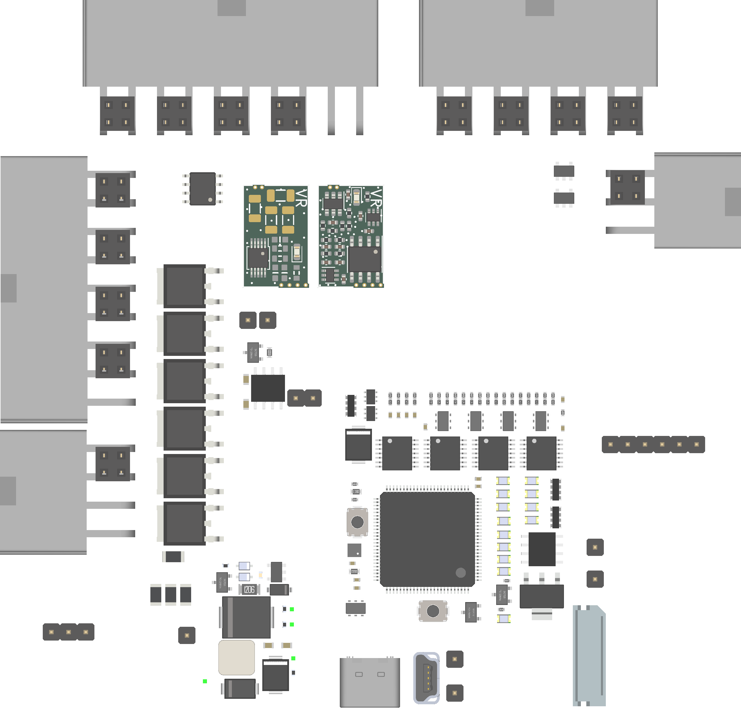
boards/uaefi-f3/board/misc/uaefi-f3-components.png
