rusefi/uaefi/boards/uaefi-a/board/uaefi-a-schematic.pdf

IGN1_(PC13) W10 | CANH | W11 CANL | W12 V33_REF W13 | V5A_SWITCHABLE W14 V5A_SWITCHABLE | W2
5569-16A2 OUT_LS_WEAK2 | OUT_IGN4

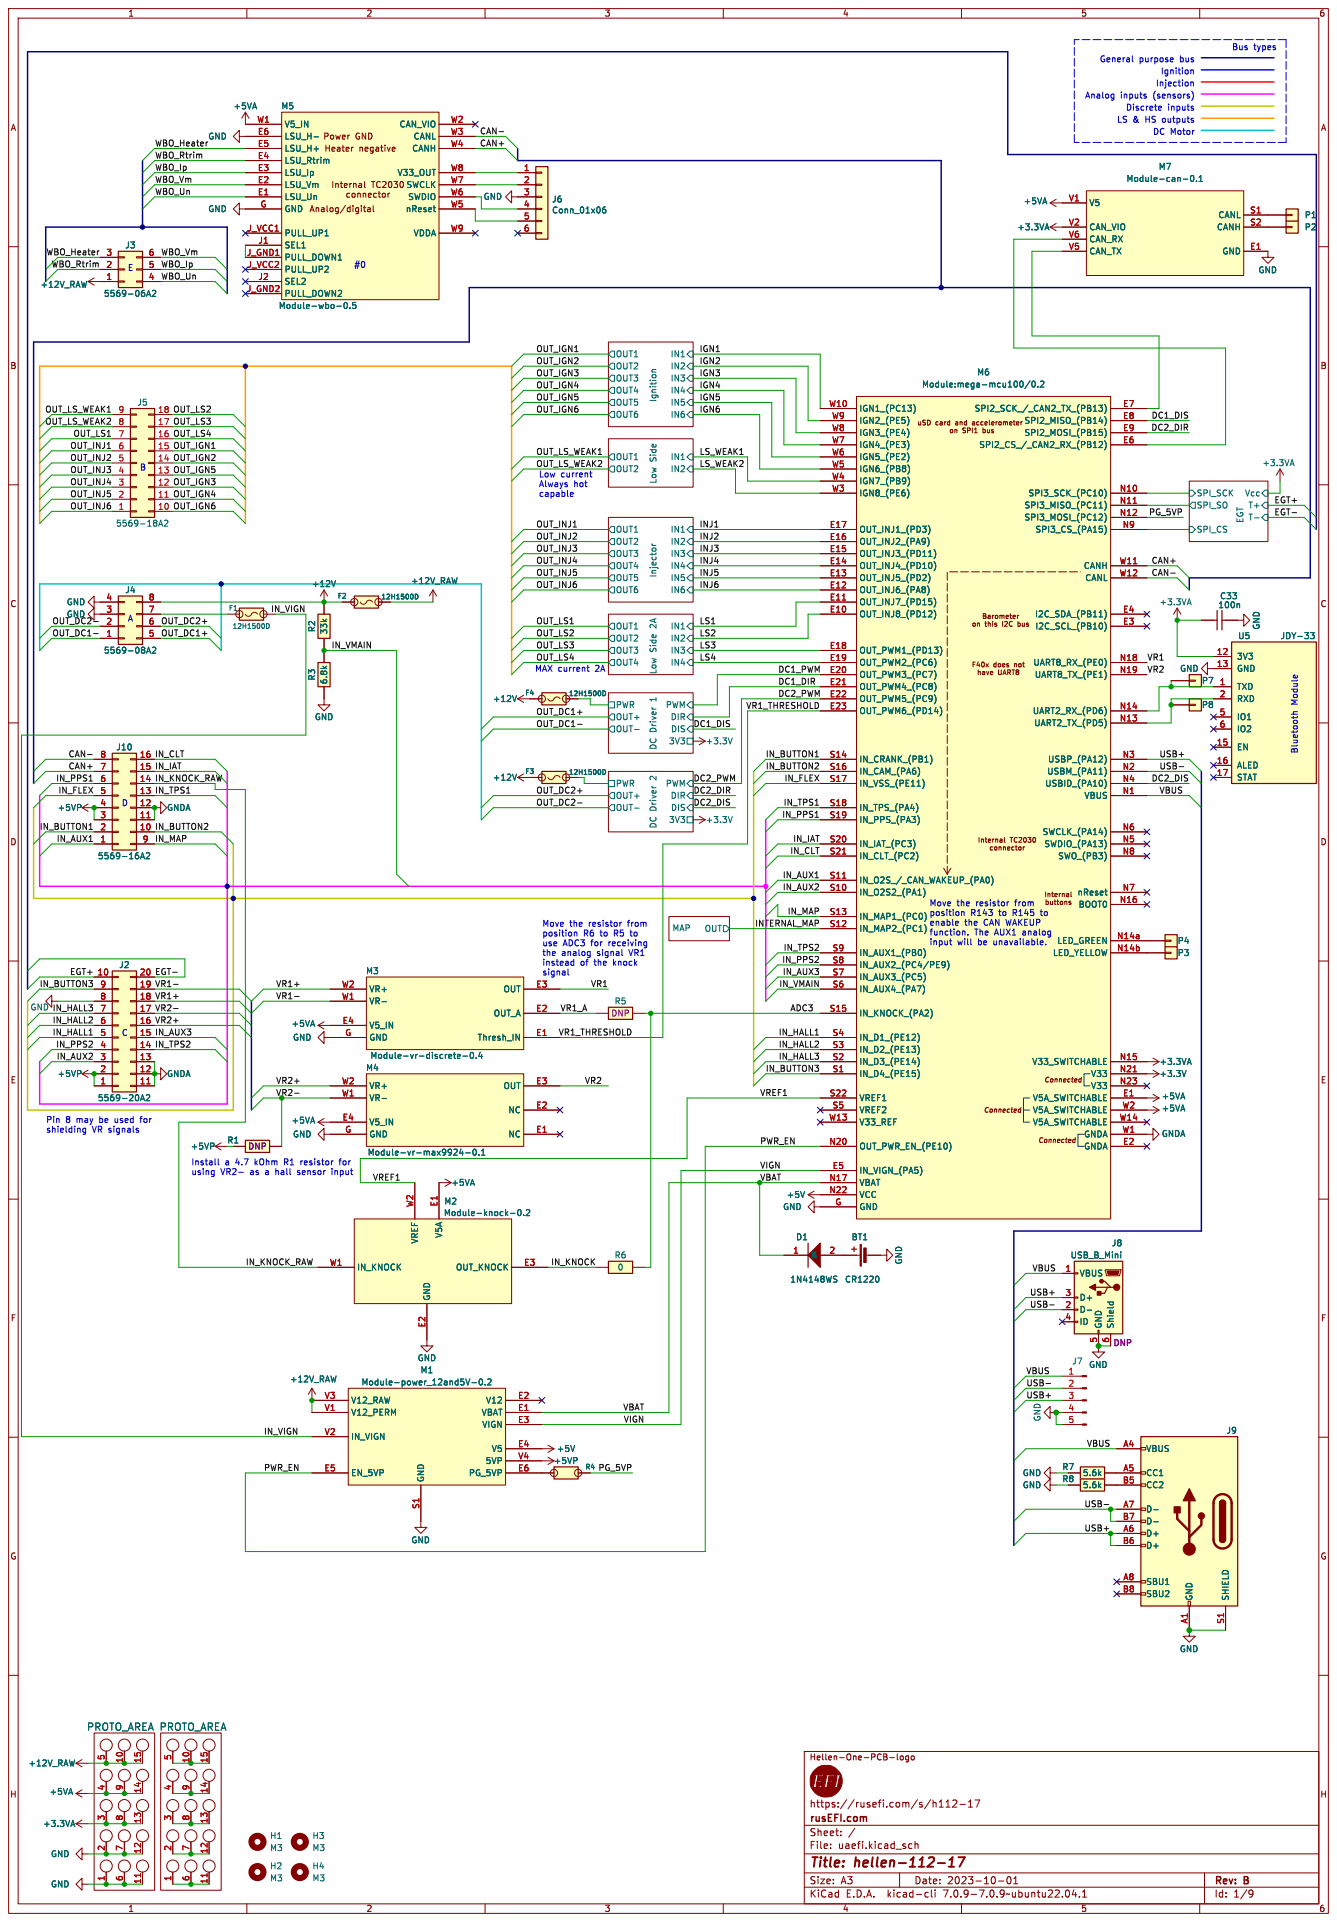
[picture p128: page 1]

LS & HS outputs Discrete inputs

Analog/digital Heater negative Power GND

3V3 12 GND 13 EN 15 ALED 16 STAT 17 RXD 2

R5 DNP GND R³ 6.8k R² 33k

enable the CAN WAKEUP
input will be unavailable.

use ADC3 for receiving
the analog signal VR1
instead of the knock
signal

https://rusefi.com/s/h112-17
File: uaefi.kicad_sch Sheet: / rusEFI.com

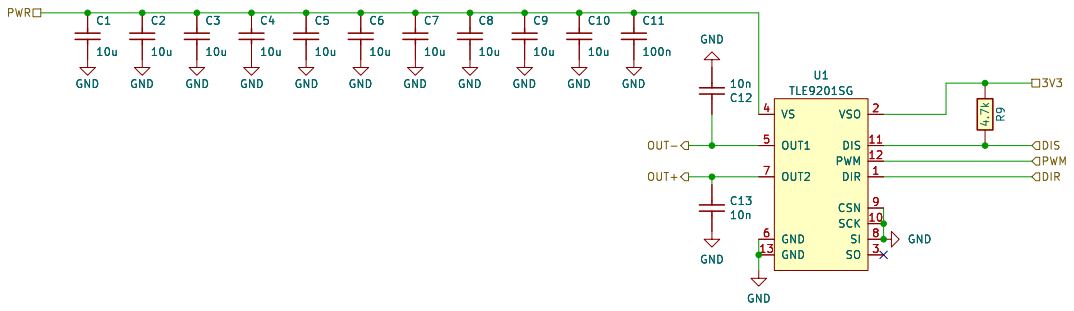
[picture p129: page 2]

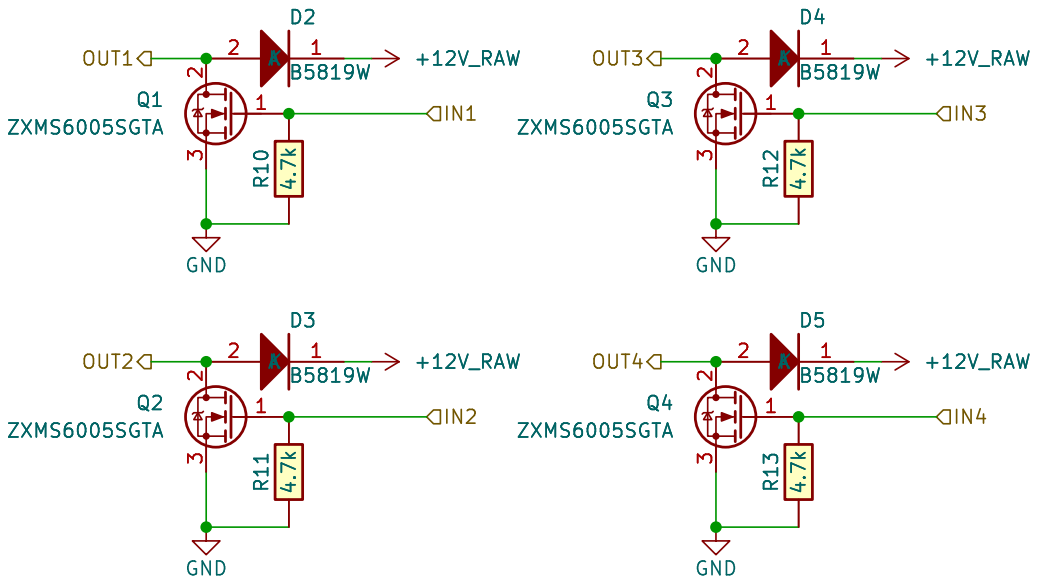
[picture p130: page 3]
D Date: 2023-11-01 KiCad; kicad-cli; 7.0.9-7.0.9~ubuntu22.04.1 Size: A4; Rev:; 2 3 Q4 ZXMS6005SGTA R10 4.7k 1; 2 3 Q1 ZXMS6005SGTA R11 4.7k K; +12V_RAW; GND; 2 3 Q3 ZXMS6005SGTA GND; +12V_RAW 1 A; D4B5819W R¹² 4.7k 1; 2 3 Q2 ZXMS6005SGTA GND; D5B5819W R¹³ 4.7k; OUT3 OUT2 OUT1; OUT4; IN3 +12V_RAW; 2 R¹³ 4.7k R¹² 4.7k; 2 Q4 ZXMS6005SGTA; 2 3 Q3 ZXMS6005SGTA; 2 3 +12V_RAW; 2 R¹¹ 4.7k R¹⁰ 4.7k Q1 ZXMS6005SGTA 1; 2 Q2 ZXMS6005SGTA

File: LS4.kicad_sch Sheet: /Low Side 2A/ rusefi.com

Id: 3/9 Title: UAEFI Low Side

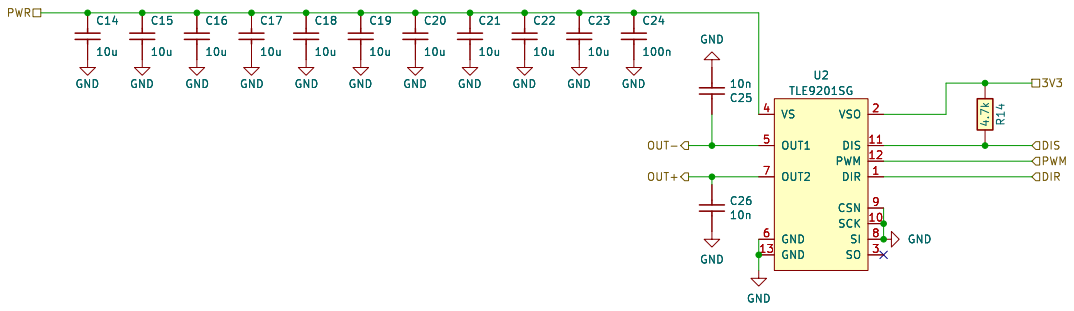
[picture p131: page 4]

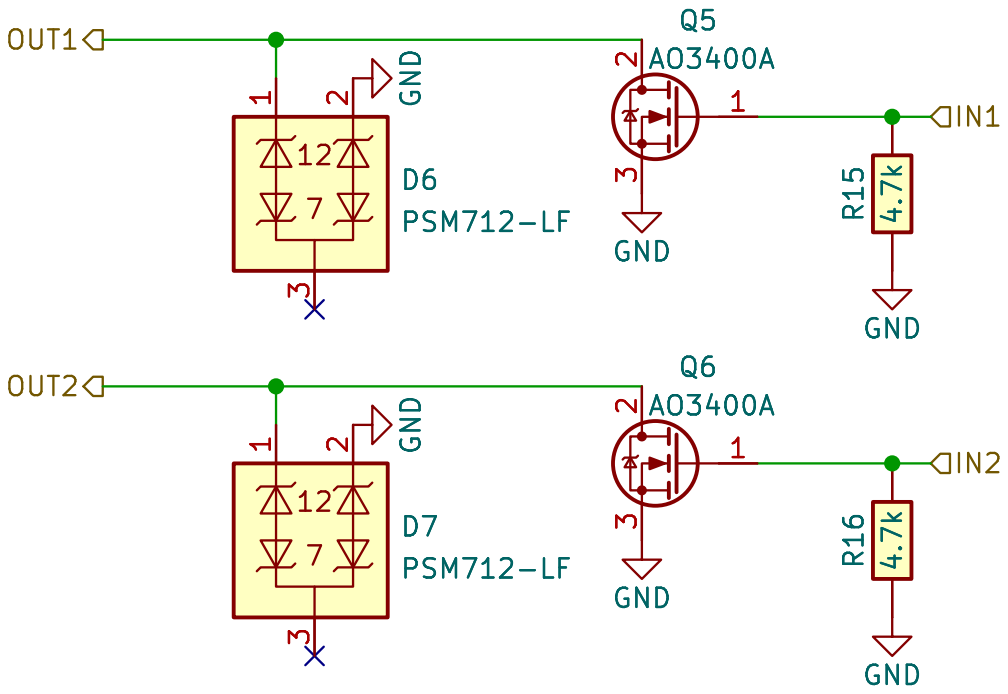
[picture p132: page 5]
D Date: 2023-11-01 KiCad; kicad-cli; 7.0.9-7.0.9~ubuntu22.04.1 Size: A4; Rev:; GND; 2 3 Q5 AO3400A GND GND; 3 D6PSM712-LF GND R16 4.7k 12; IN1 OUT1 OUT2; 2 3 GND GND; D6PSM712-LF; 3 D7PSM712-LF; 2 3 GND

3 D7PSM712-LF GND GND R15 4.7k

3 GND GND R15 4.7k R16 4.7k GND Q6 AO3400A

Id: 6/9 Title: UAEF Low Side low current File: LS_weak.kicad_sch Sheet: /Low Side/ rusefi.com

D Date: KiCad; kicad-cli; 7.0.9-7.0.9~ubuntu22.04.1 Size: A4; Rev:; VOUT; 1 GND; 2 VCC; 6 U3 MPX4/MPXH6400_MAP; GND GND; OUT U3 MPX4/MPXH6400_MAP

Id: 8/9 Title: File: MAP.kicad_sch Sheet: /MAP/

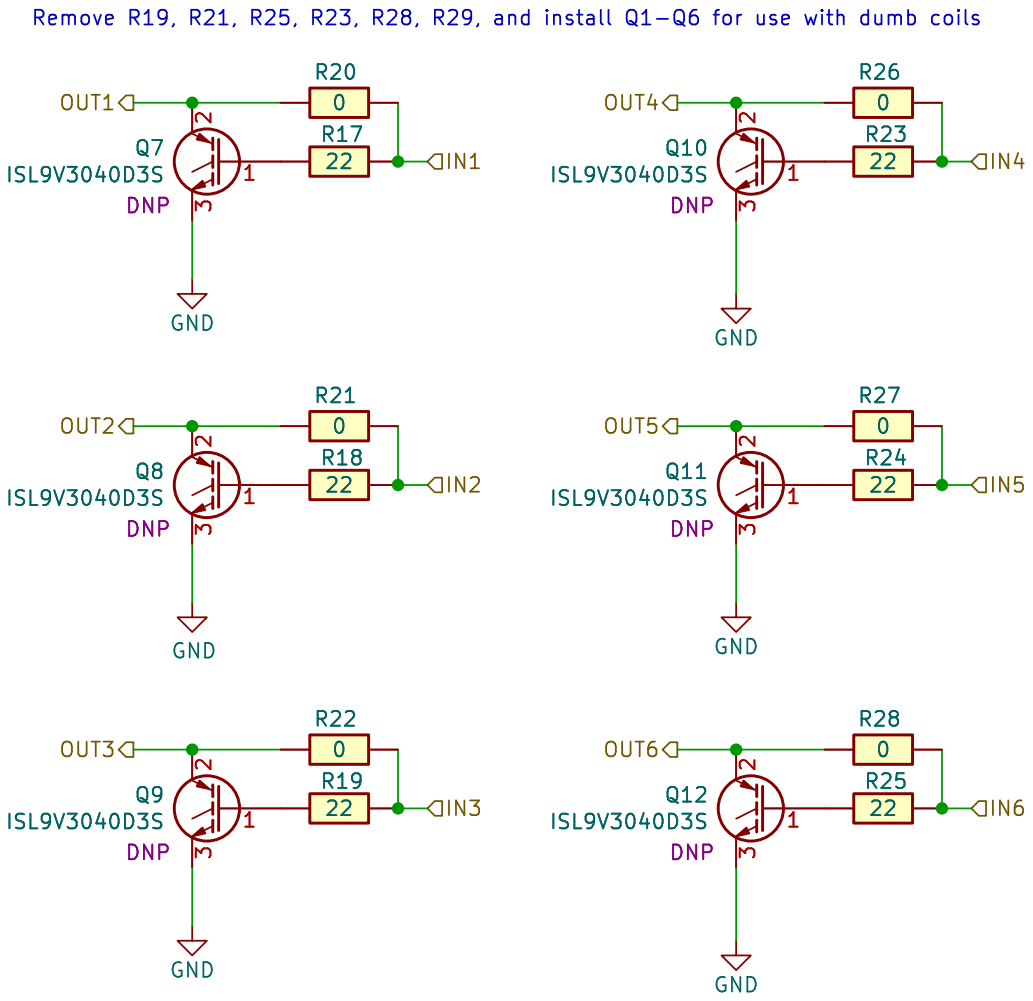
[picture p133: page 7]

File: IGN6.kicad_sch Sheet: /Ignition/ rusefi.com

Id: 9/9 Title: UAEFI Ignition


4 SCK 5 ~{CS}6 SO 7 U4 MAX31855KASA DNP

Id: 9/9 Title: File: egt.kicad_sch Sheet: /EGT/

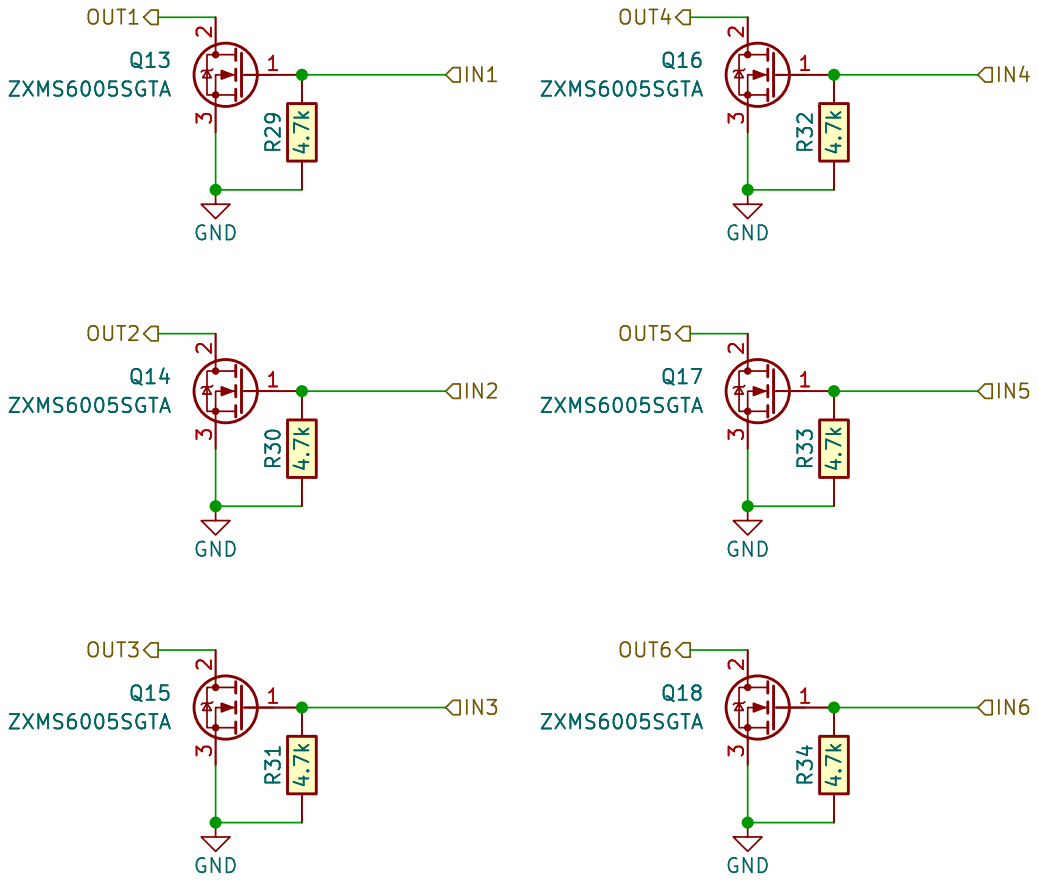
[picture p134: page 9]

Id: 10/9 Title: UAEFI Injector File: INJ6.kicad_sch Sheet: /Injector/ rusefi.com


Hellen One : Power-Module interface

Reverse polarity and overvoltage protection
F410 V12_RAW


## +5VGND

## +5VGND


Outputs a pulse on rising edge R751

Vref generation RS Latch Tracks which edge happened last
4 GND GND

Differential to single ended conversion

Outputs a pulse on falling edge


Id: 1/1 Title: VR MAX9924 module

+3.3V C616

27k +


100n GND GND R⁶⁰⁸ ⁴⁷

1 PA4 10 PA5 11 PA6 12 PA7 13 PB0 14 PB1 15 VSS 16 VDDIO2 17 PA8 18 PA9 19 PF0 2 PA10 20 PA11 21 PA12 22 PA13 23 PA14 24 PA15 25 PB3 26 PB4 27 PB5 28 PB6 29 PF1 3 PB7 30 PB8 31 VSSA 32 NRST 4 VDDA

1u GND GND GND
+3.3V R⁶¹¹ ²⁰k R⁶¹⁰ ²⁰k GND

to ground to improve the routing
(floating pins by the software).

Heater negative Power GND

VDDA GND
Nernst Sense Voltage Buffer Nernst Internal Resistance Measurement

+3.3V C606 DNP GND
File: hellen1-wbo.kicad_sch Sheet: / rusefi.com V⁻ 11 V⁺

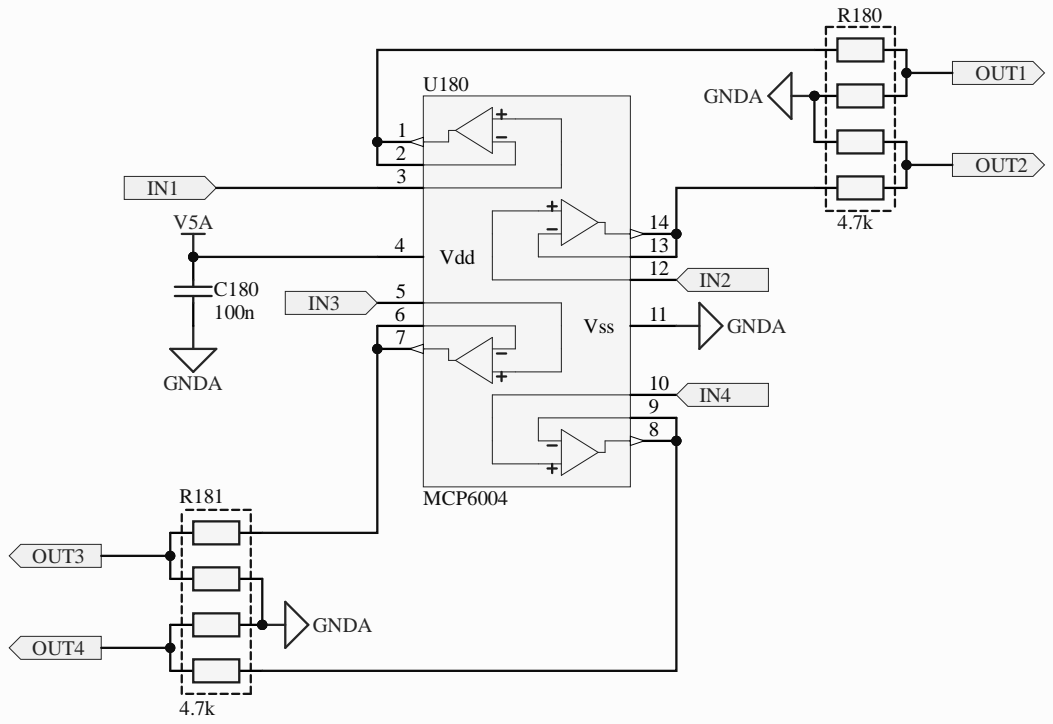
[picture p135: page 15]
Vdd 4; Vss 6; MCP6004; GNDA; OUT1; OUT2; OUT3; OUT4; C180 PIC18001 100n; PIC18002 COC3; PIR18001; PIR18002; PIR18003; PIR18004; PIR18005; PIR18006; PIR18007; PIR18008; COR5; PIR18101; PIR18102; PIR18103; PIR18105; PIR18104; PIR18106; PIR18107; PIR18108; COR6; PIU18001; PIU18002; PIU18003; PIU18004; PIU18005; PIU18006; PIU18007; PIU18008; PIU18009; PIU180010; PIU180011; PIU180012; PIU180013; PIU180014; COU2; PIC18001; POOUT2; POOUT1; POOUT3; POOUT4; POIN1; POIN3 PIU18005; PIU180010 POIN4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

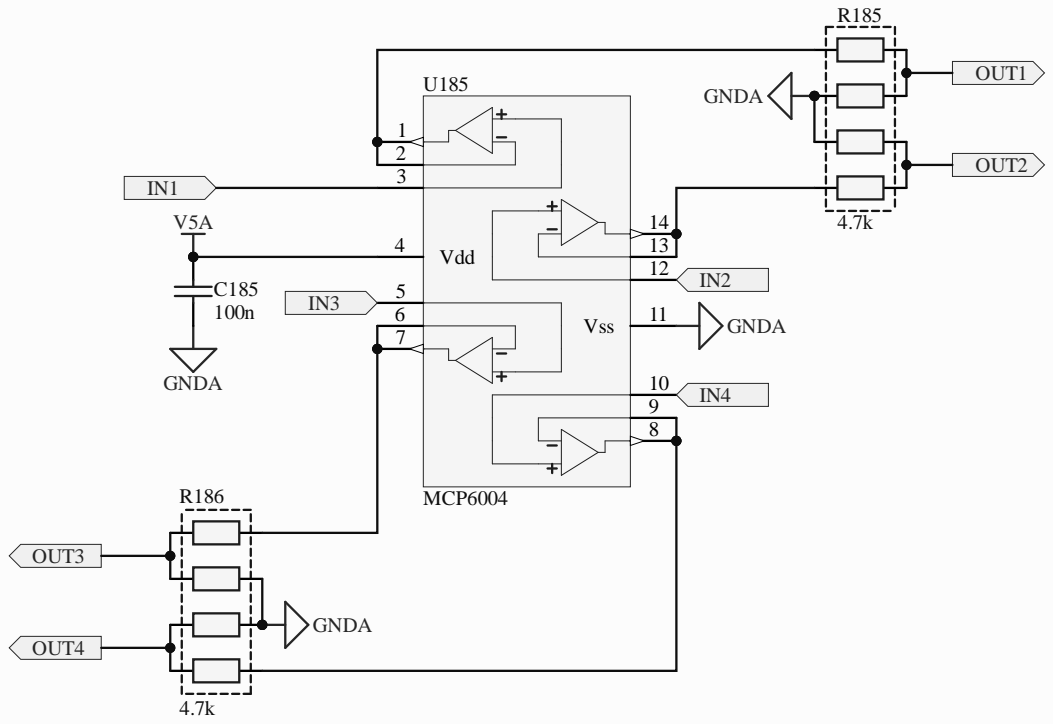
[picture p136: page 16]
Vdd 4; Vss 6; MCP6004; GNDA; OUT1; OUT2; OUT3; OUT4; C185 PIC18501 100n; PIC18502 COC3; PIR18501; PIR18502; PIR18503; PIR18504; PIR18505; PIR18506; PIR18507; PIR18508; COR5; PIR18601; PIR18602; PIR18603; PIR18605; PIR18604; PIR18606; PIR18607; PIR18608; COR6; PIU18501; PIU18502; PIU18503; PIU18504; PIU18505; PIU18506; PIU18507; PIU18508; PIU18509; PIU185010; PIU185011; PIU185012; PIU185013; PIU185014; COU2; PIC18501; POOUT2; POOUT1; POOUT3; POOUT4; POIN1; POIN3 PIU18505; PIU185010 POIN4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

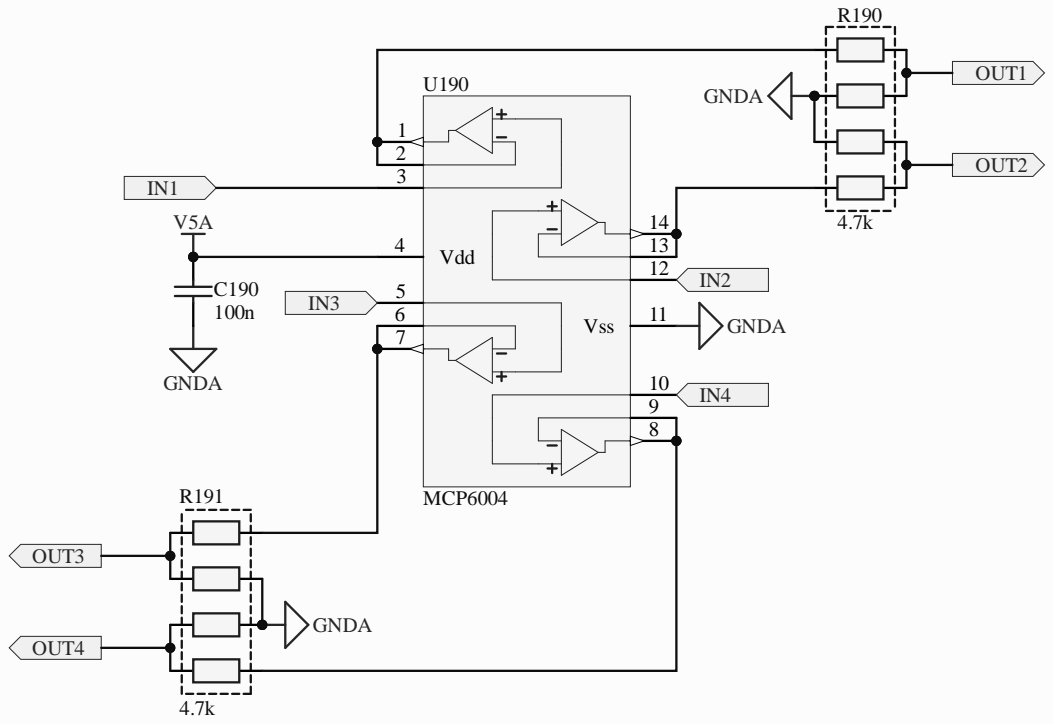
[picture p137: page 17]
Vdd 4; Vss 6; MCP6004; GNDA; OUT1; OUT2; OUT3; OUT4; C190 PIC19001 100n; PIC19002 COC3; PIR19001; PIR19002; PIR19003; PIR19004; PIR19005; PIR19006; PIR19007; PIR19008; COR5; PIR19101; PIR19102; PIR19103; PIR19105; PIR19104; PIR19106; PIR19107; PIR19108; COR6; PIU19001; PIU19002; PIU19003; PIU19004; PIU19005; PIU19006; PIU19007; PIU19008; PIU19009; PIU190010; PIU190011; PIU190012; PIU190013; PIU190014; COU2; PIC19001; POOUT2; POOUT1; POOUT3; POOUT4; POIN1; POIN3 PIU19005; PIU190010 POIN4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

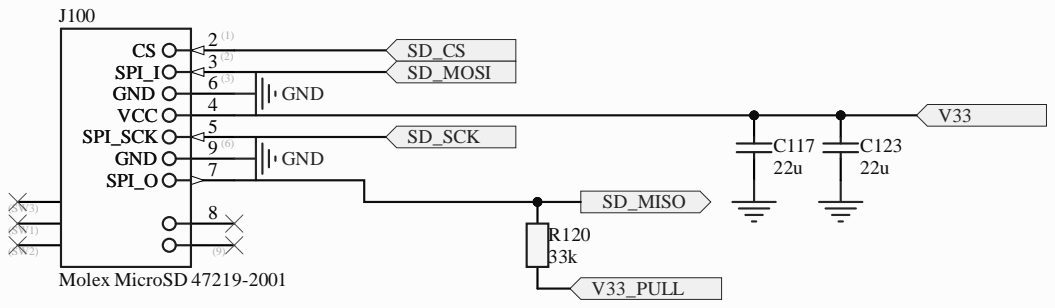
[picture p138: page 18]
SPI_; VCC; 5 SPI_SCK; 7 SPI_O; lex MicroSD; _MIS

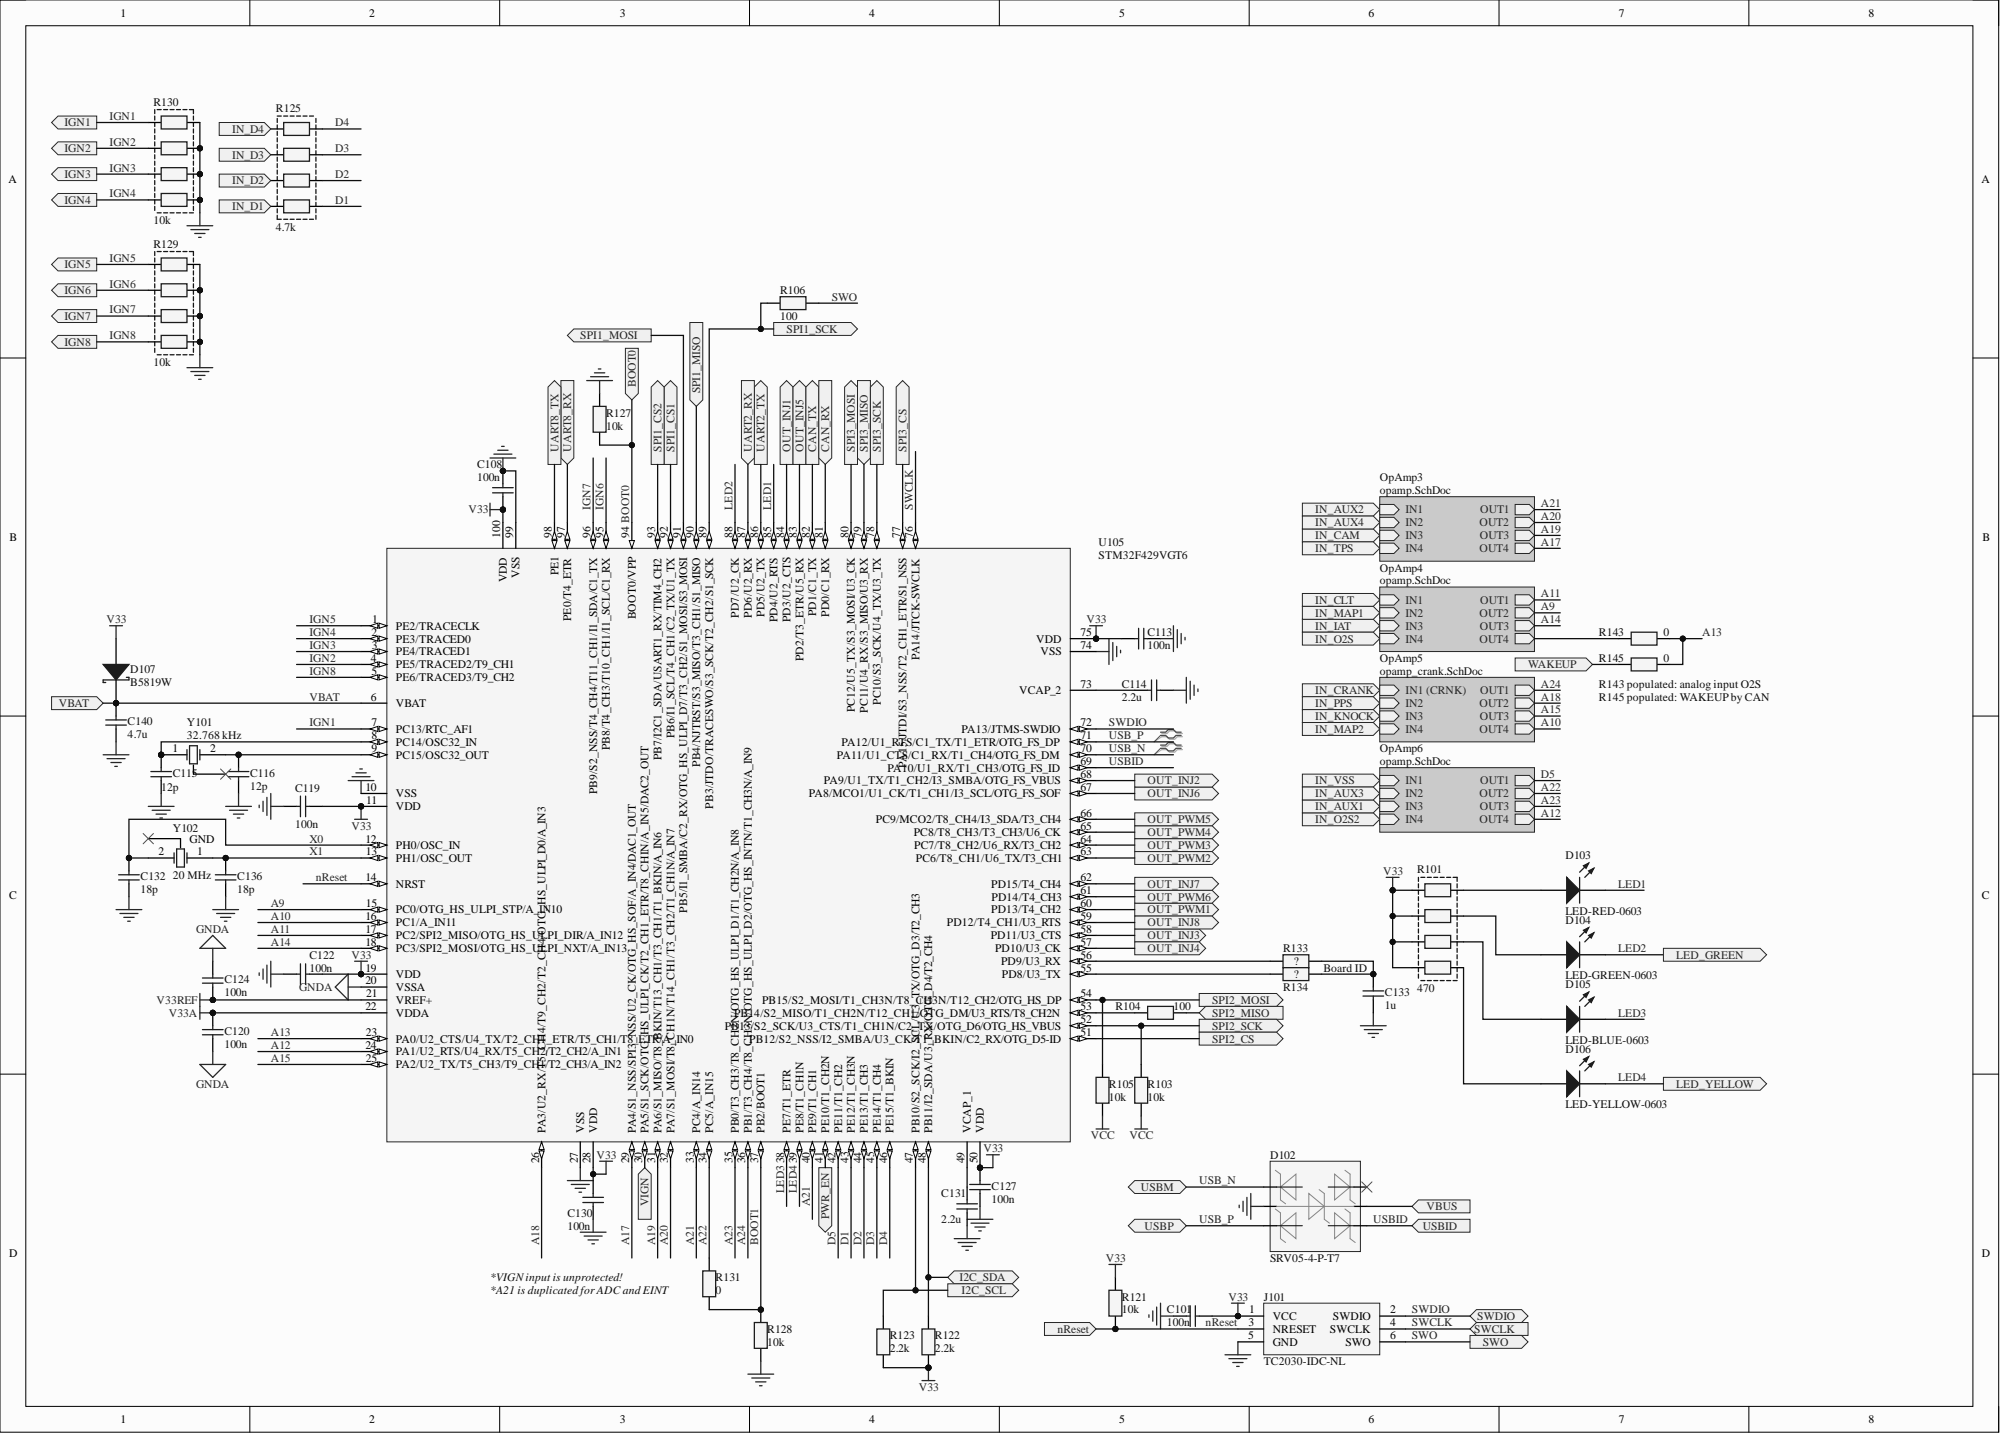
[picture p139: page 19]

R143 populated: analog input O2S
R145 populated: WAKEUP by CAN

*VIGN input is unprotected!
*A21 is duplicated for ADC and EINT

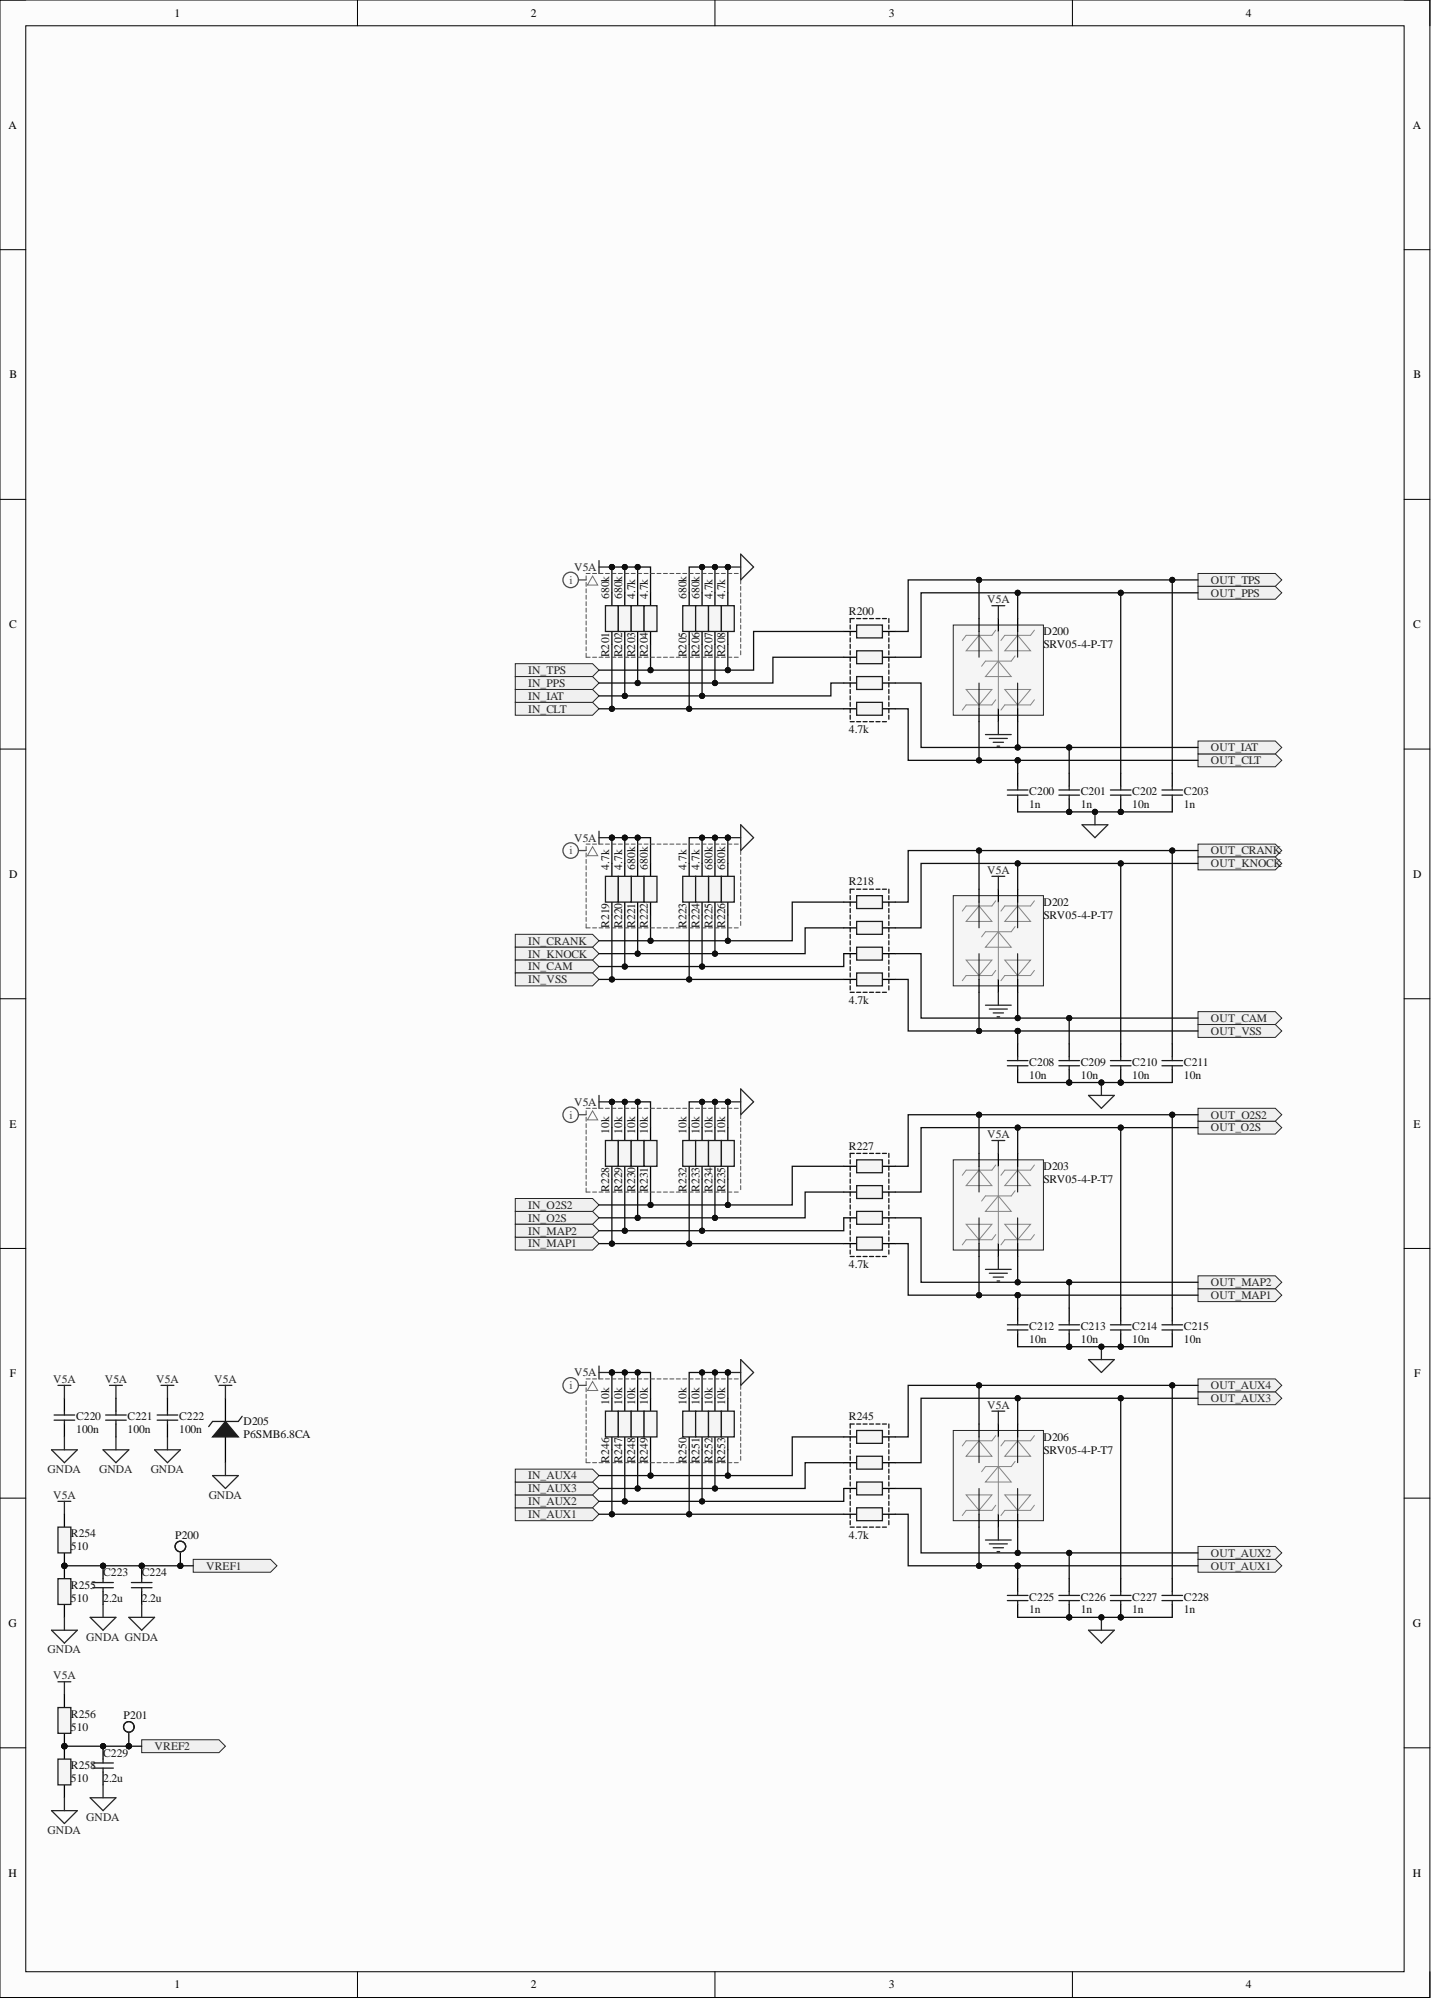
[picture p140: page 20]

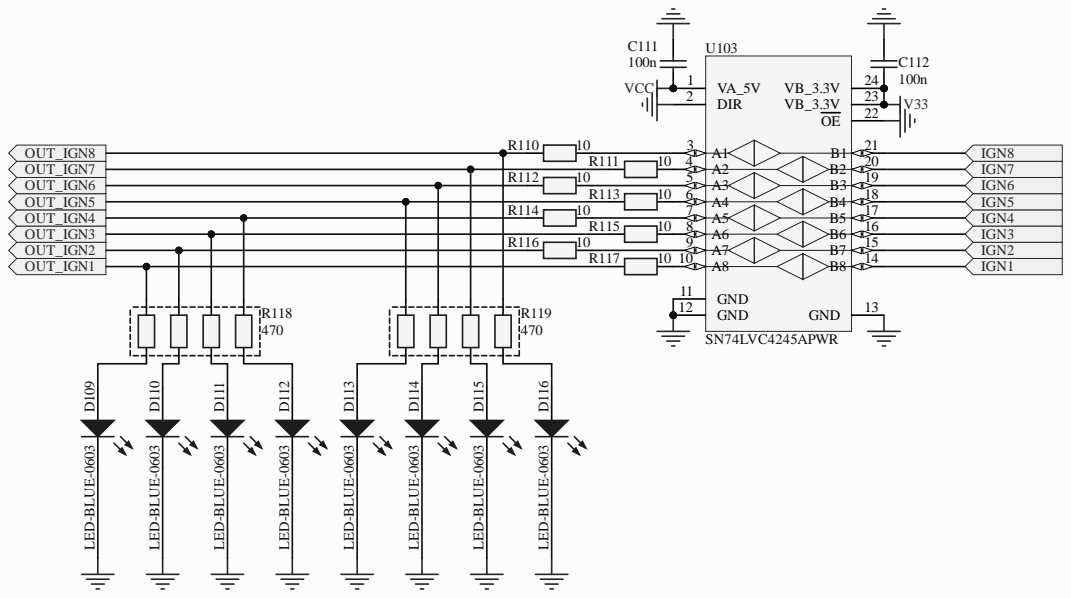
[picture p141: page 21]

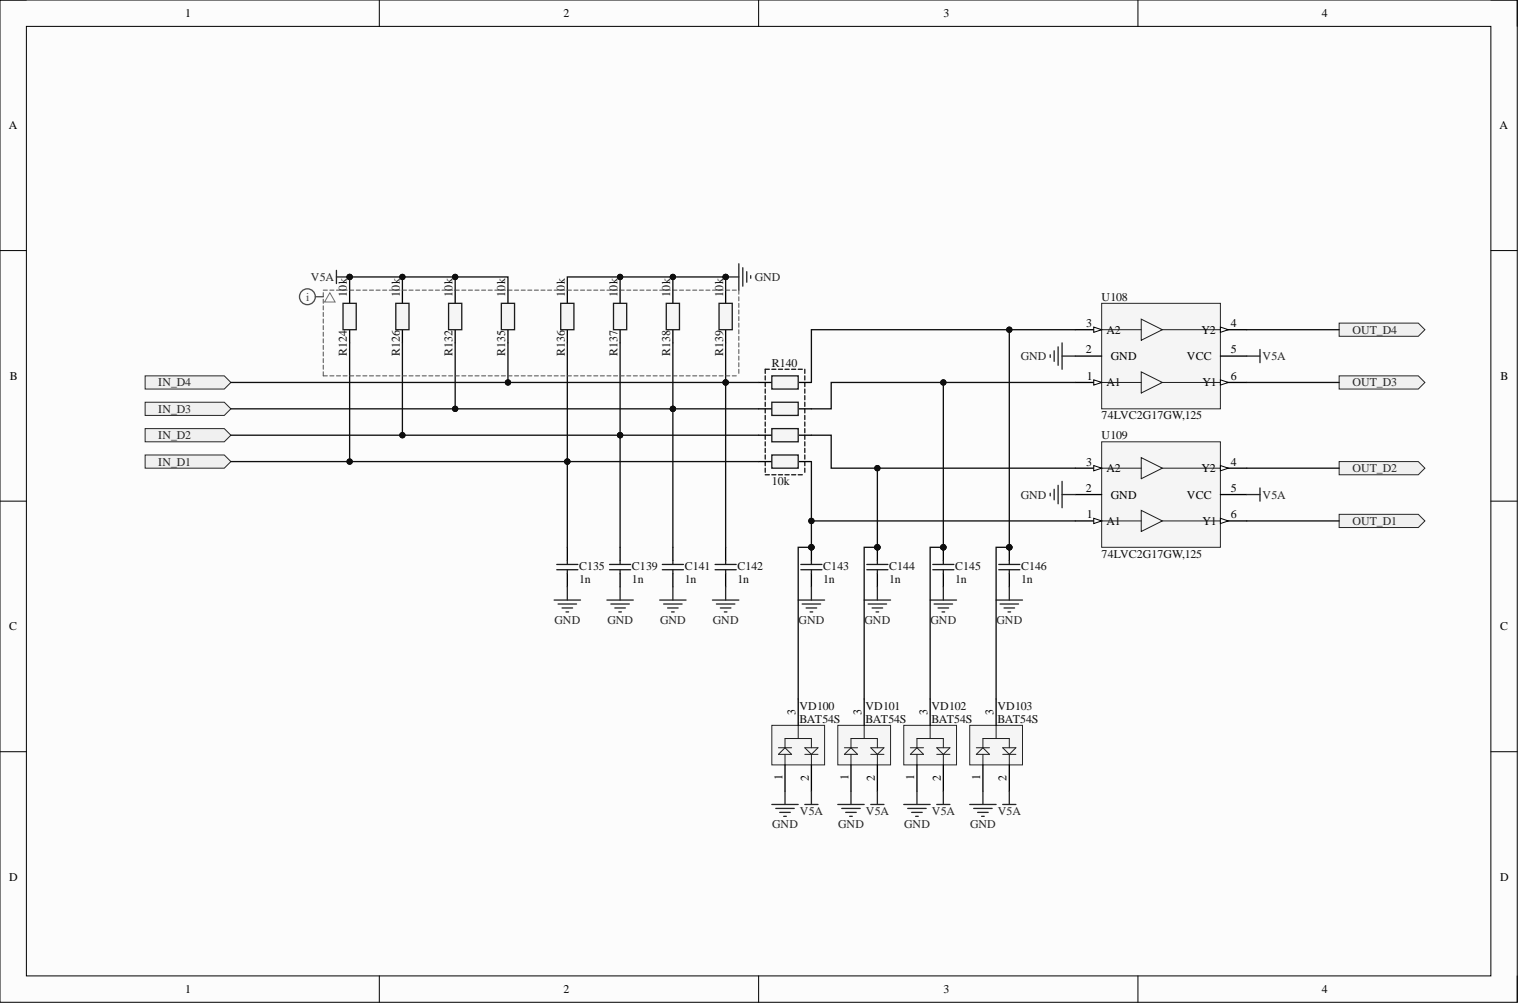
[picture p142: page 22]

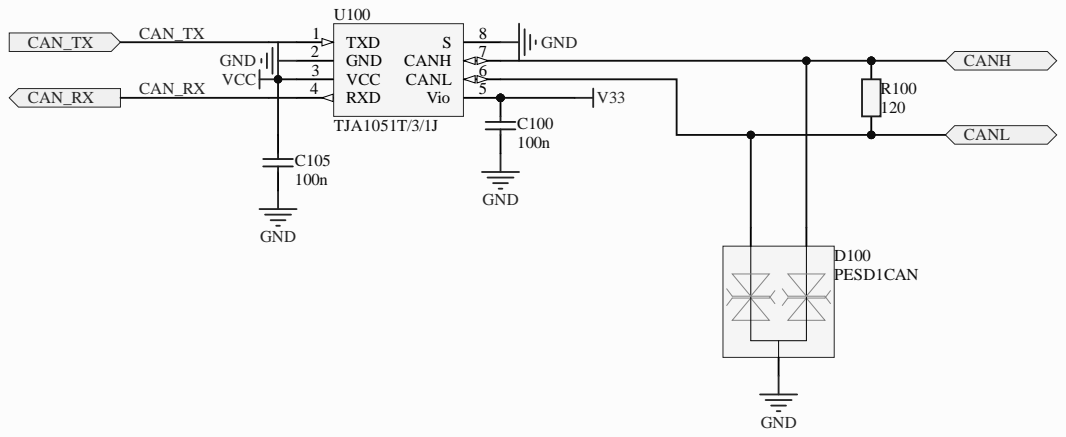
[picture p143: page 23]
D100 PESD1CAN; GND; TXD 1 GND 2 VCC 3; Vio; 5 RXD 4; CANL; 6 CANH; TJA1051T/3/1J; CAN_TX; CAN_RX; VCC; CANH; CANL C100 100n

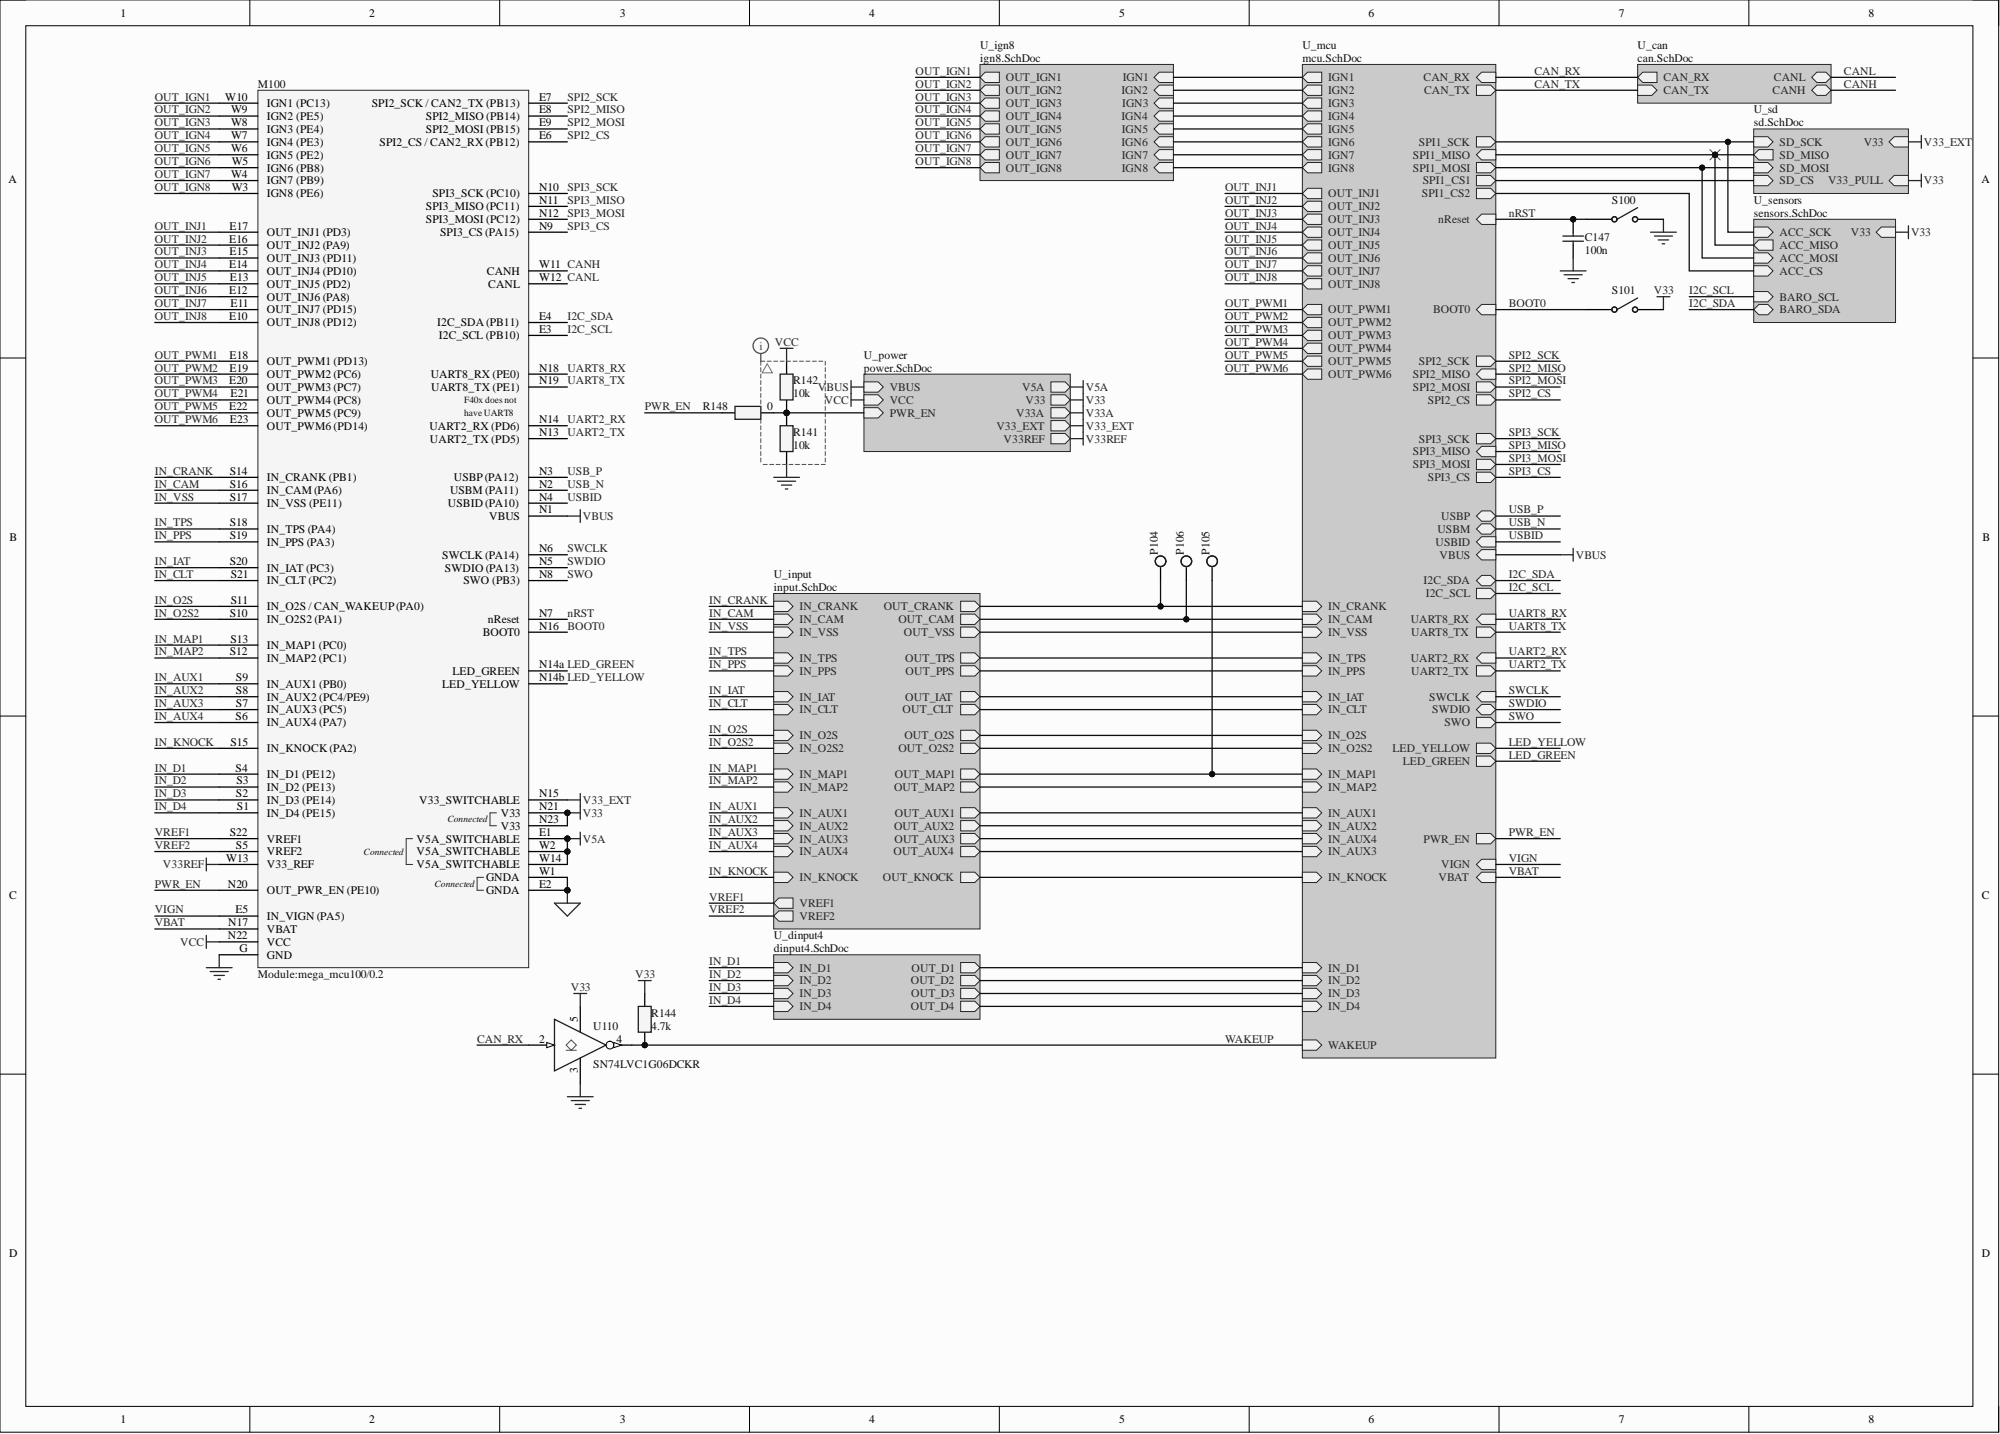
[picture p144: page 24]
VRE; _CRA; _CLT; IAT; _IAT; VIG; nRes; VBAT; SWCL; SPI2; _MIS; SPI3; I2C_SCL; SPI1; PWR_; GRE; u mcu.Sch; _IGN; 8.Sch; n can.Sch; d.Sch; nRS; USB_; P USB_; USBI; A I2C_SCL UART8_RX UART8_TX UART2_RX UART2_TX; N VBAT; VCC; ACC_SC; ACC_; ACC_MIS; ACC_MO; BARO; sen; ors.Sc; LVC1; VBU; wer.Sch; USBID (PA; USBM (PA; USBP (PA; 8 SWDIO (PA13); N5 SWCLK (PA14); N6 nReset; _SCK (PC1; _MISO (PC1; _MOSI (PC1; I2C_SCL (PB1; 3 I2C_SDA (PB11); E4 UART2_TX (PD5); _SCK; _MISO (PB1; _MOSI (PB1; _PWM2 (PC6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

USBM USBP USBID VBUS

### COR2

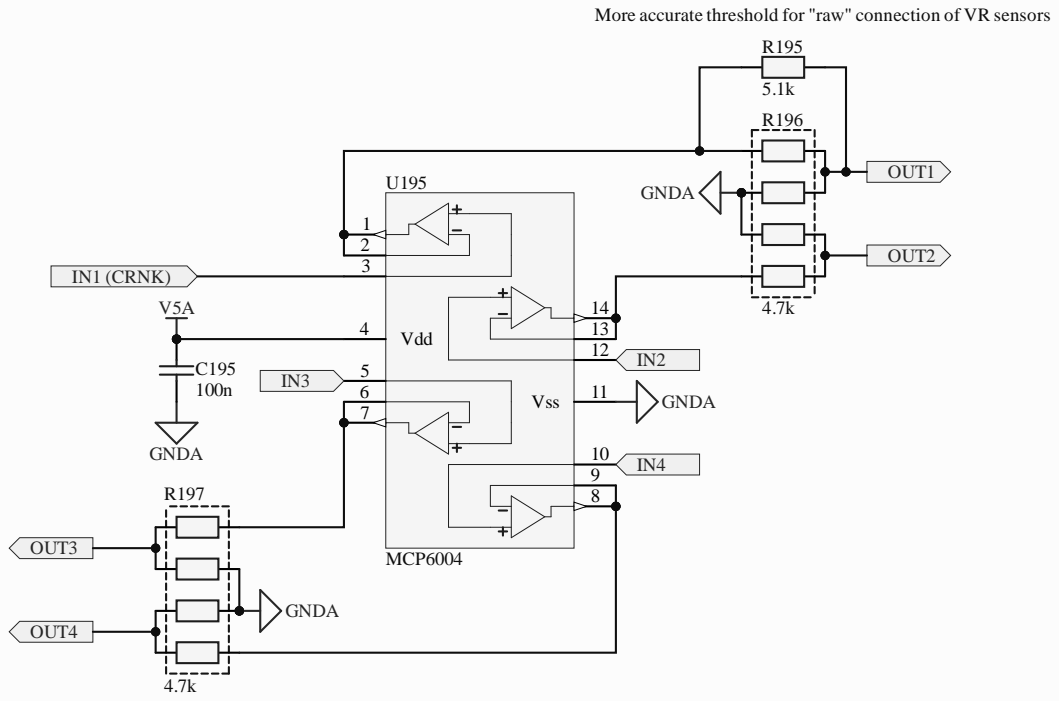
[picture p145: page 25]
Vdd 4; Vss 6; MCP6004; GNDA; IN1 (CRNK); OUT1; OUT2; OUT3; OUT4; C195 PIC19501 100n; PIC19502 COC2; PIR19502; PIR19501; PIR19601; PIR19602; PIR19603; PIR19604; PIR19605; PIR19606; PIR19607; PIR19608; COR3; PIR19701; PIR19702; PIR19703; PIR19705; PIR19704; PIR19706; PIR19707; PIR19708; COR4; PIU19501; PIU19502; PIU19503; PIU19504; PIU19505; PIU19506; PIU19507; PIU19508; PIU19509; PIU195010; PIU195011; PIU195012; PIU195013; PIU195014; COU1; PIC19501; POOUT1; POOUT2; POOUT3; POOUT4; POIN1 (CRNK)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

More accurate threshold for "raw" connection of VR sensors

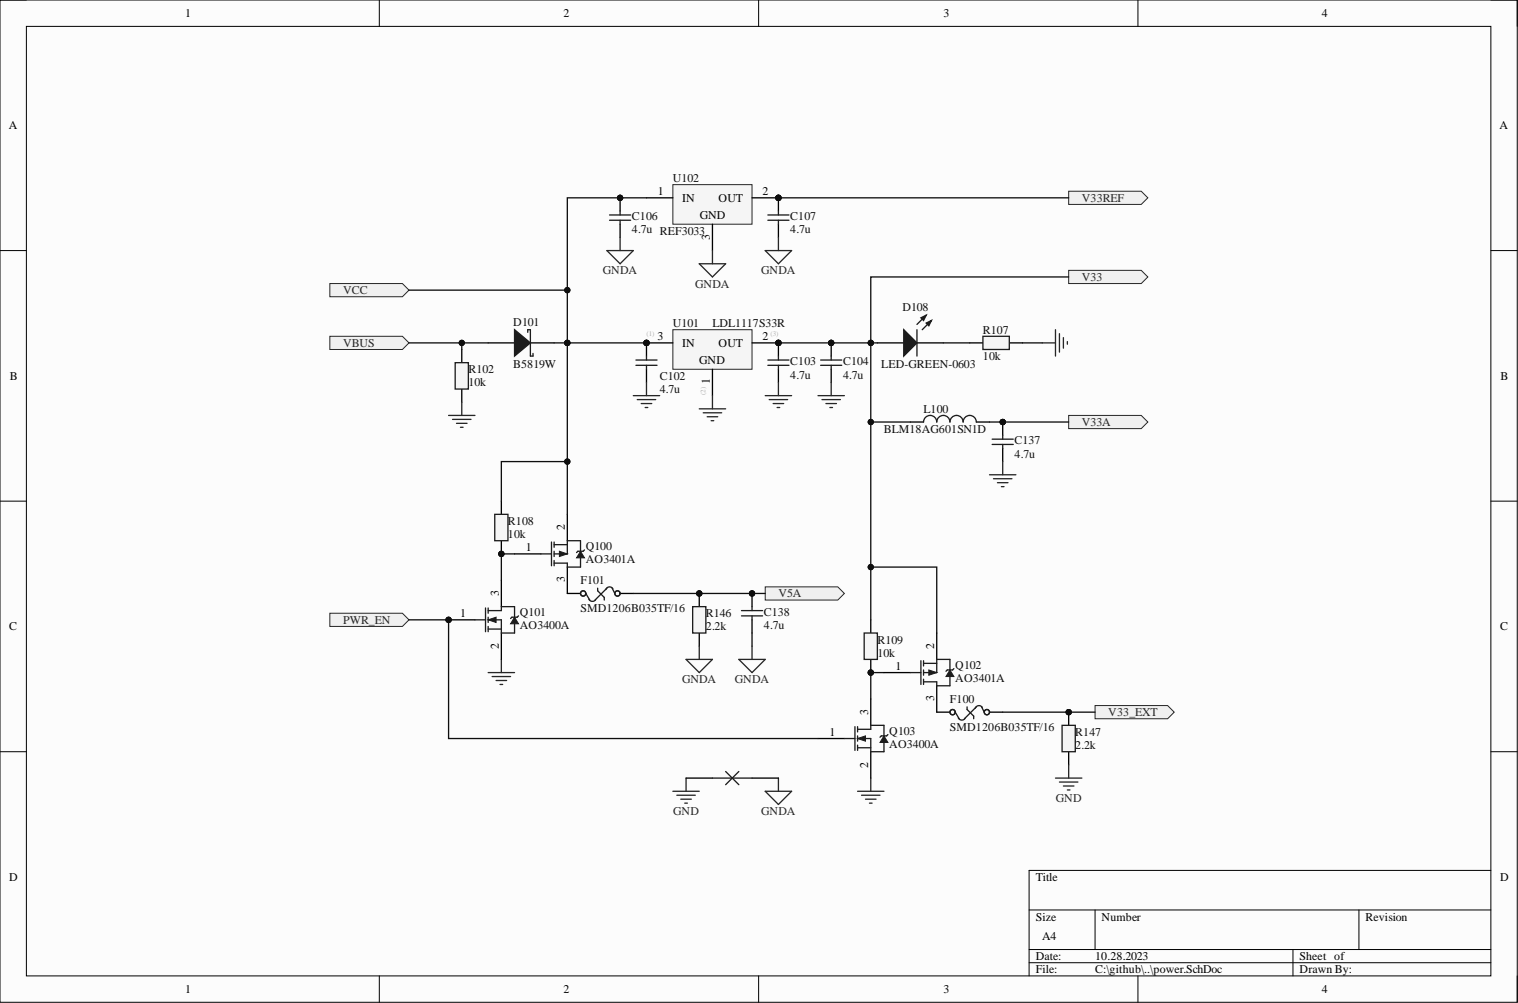
[picture p146: page 26]

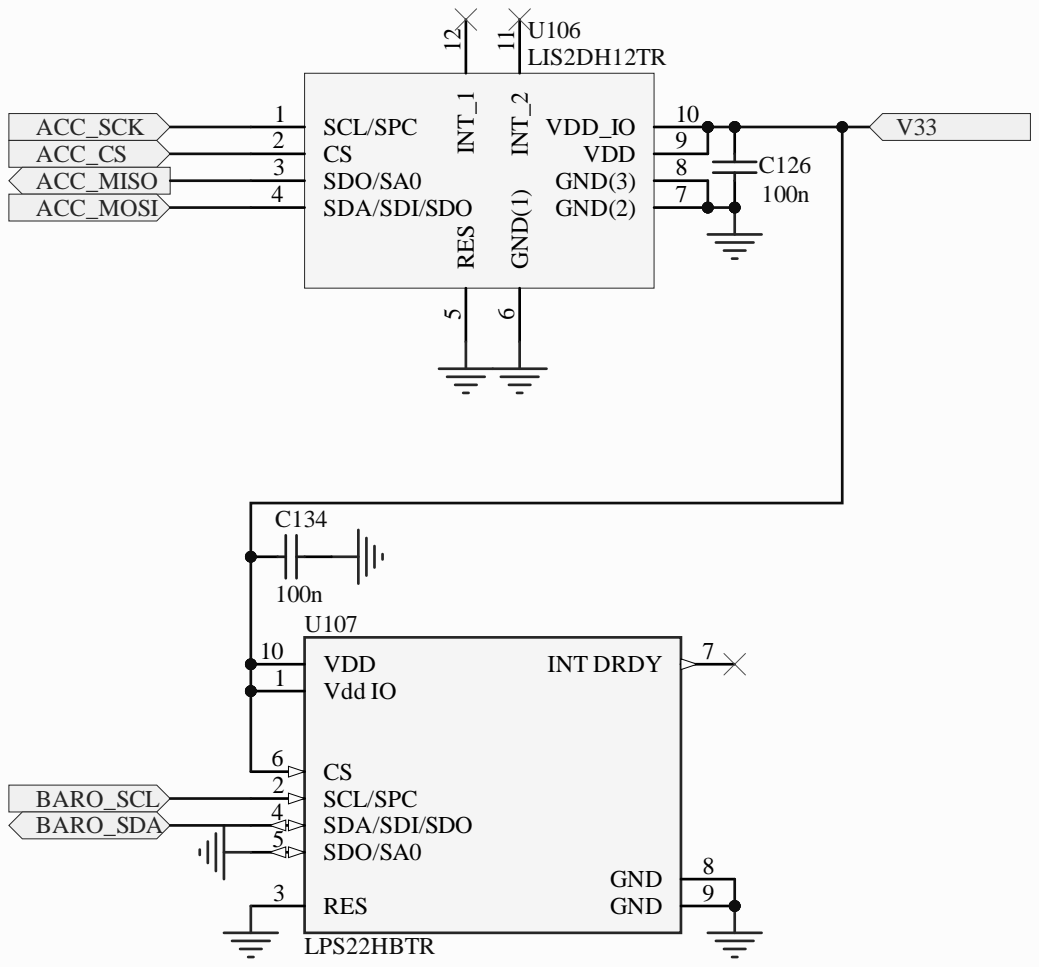
[picture p147: page 27]
RES 5; GND(1) 6; GND(2); 7 GND(3); 8 VDD; 9 VDD_IO; INT_2 11; INT_1 12; U106 LIS2DH12TR; VDD 10; INT DRDY; RES 3; Vdd IO 1; GND; LPS22HBTR; ACC_SCK ACC_CS ACC_MISO ACC_MOSI; BARO_SCL BARO_SDA

SCL/SPC 1
SDO/SA0 3
SDA/SDI/SDO 4

SCL/SPC 2
SDO/SA0 5

andreika; Size:; Author:; Date:; Revision:; Sheet; PESD1CAN; GND; CANH; CANL; TXD 1 GND 2 VCC 3; Vio; 5 RXD 4; 6 CANH; TJA1051T/3/1J; CANH CANL; CAN_TX; CAN_RX; CAN_VIO; CAN_VIO V2; S2 CANL; CAN_TX V5; CAN_RX V6; Module:can/0.1

Hellen-One CAN
Title:

rusEFI EMS
Hellen-One Platform
https://rusefi.com/s/hellen72
